aderusha/DDD-Printable-Wall-Control-System/images/Recipies/belt-clip-hanger-empty.jpg

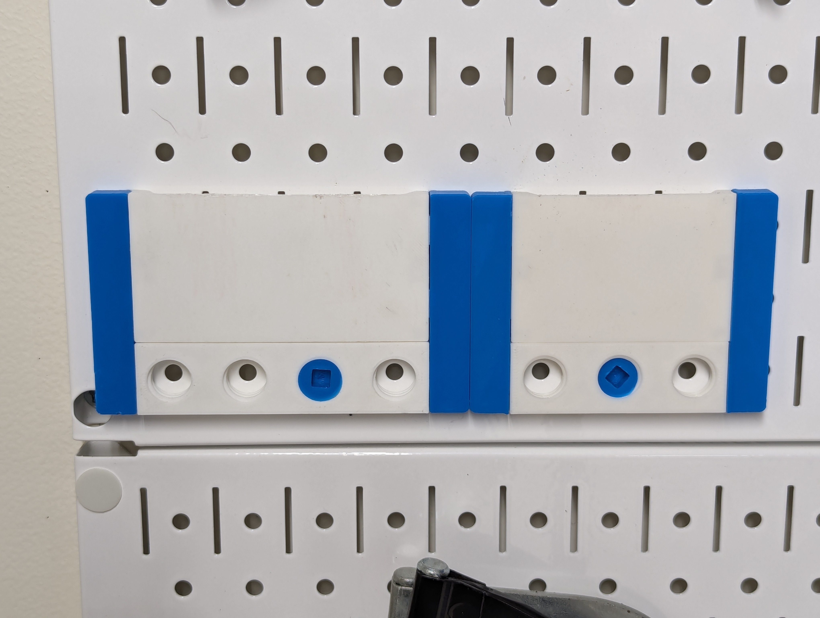
images/Recipies/belt-clip-hanger-empty.jpg
