aderusha/DDD-Printable-Wall-Control-System/images/Recipies/belt-clip-hanger-populated.jpg

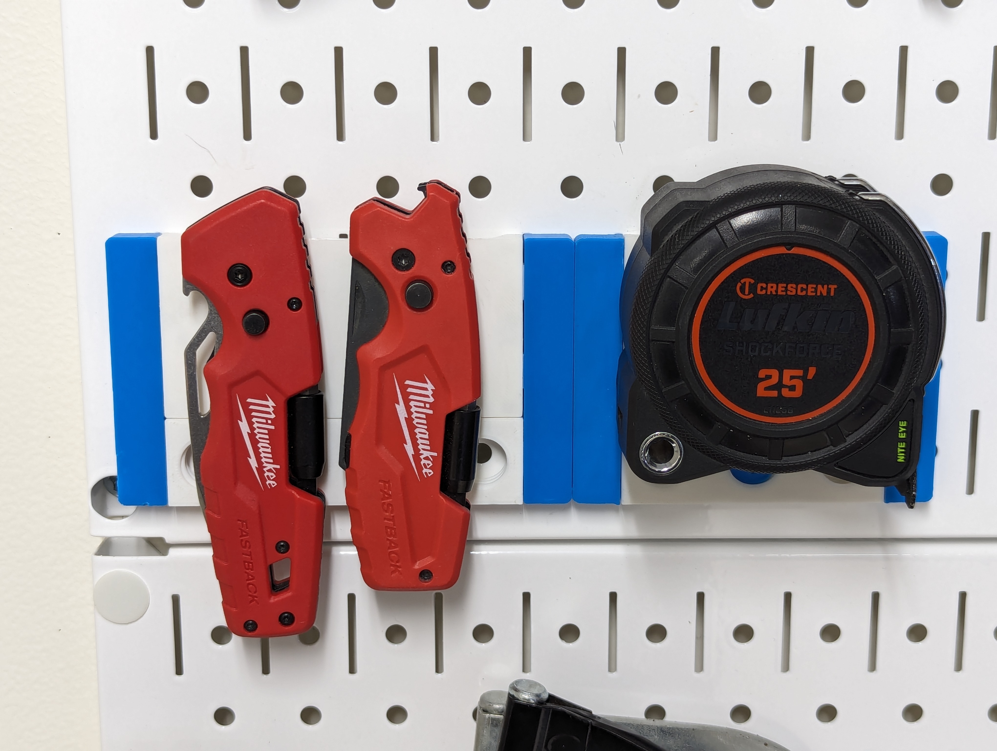
images/Recipies/belt-clip-hanger-populated.jpg
