aderusha/DDD-Printable-Wall-Control-System/images/Recipies/DeWalt-DCF923-populated.jpg

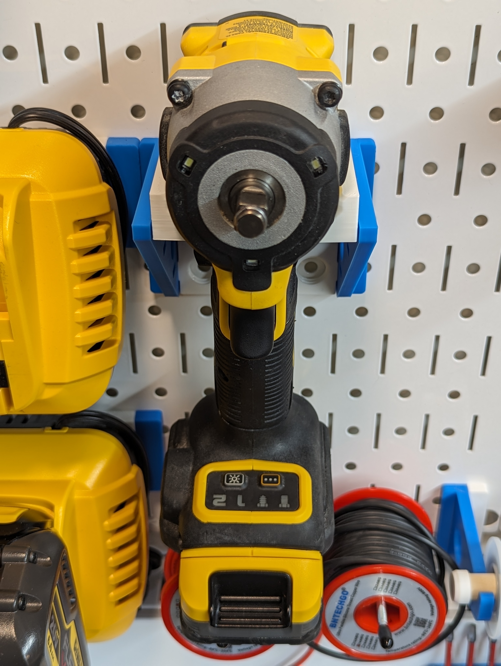
images/Recipies/DeWalt-DCF923-populated.jpg
