aderusha/DDD-Printable-Wall-Control-System/images/Vertical_vs_Horizontal_Wall_Control_Patterns.png

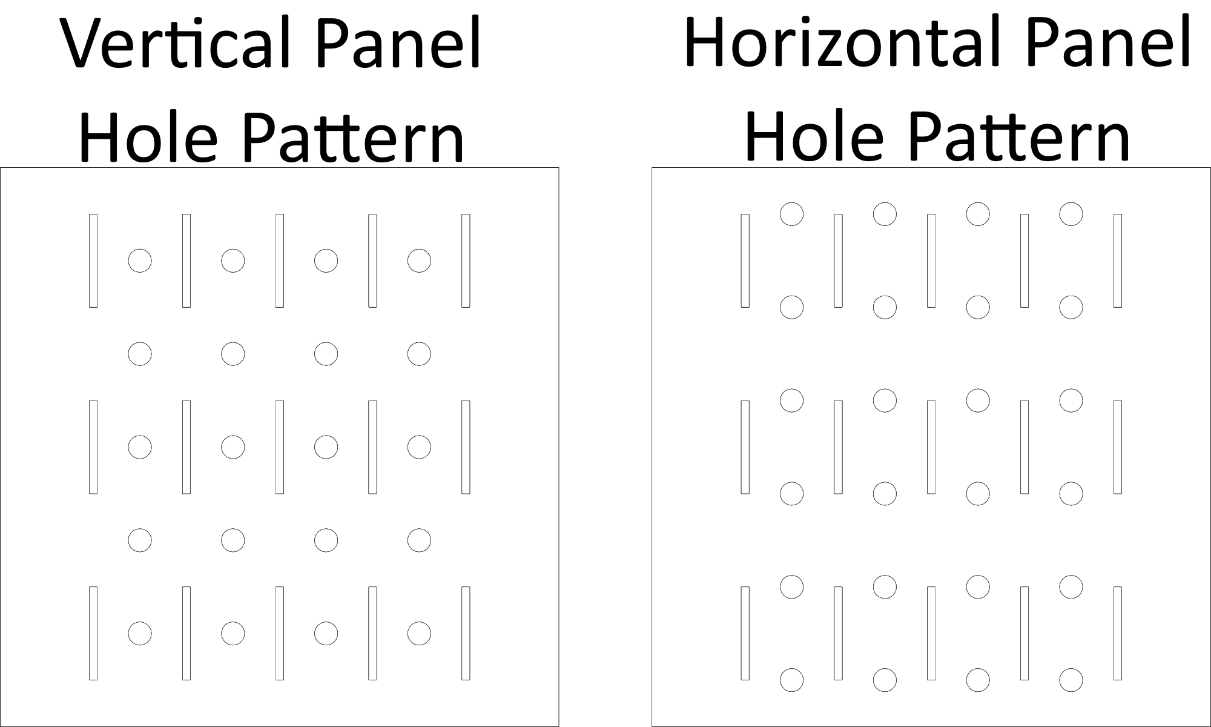
images/Vertical_vs_Horizontal_Wall_Control_Patterns.png
