aderusha/DDD-Printable-Wall-Control-System/images/WallControls-HuskyDrivers.jpg

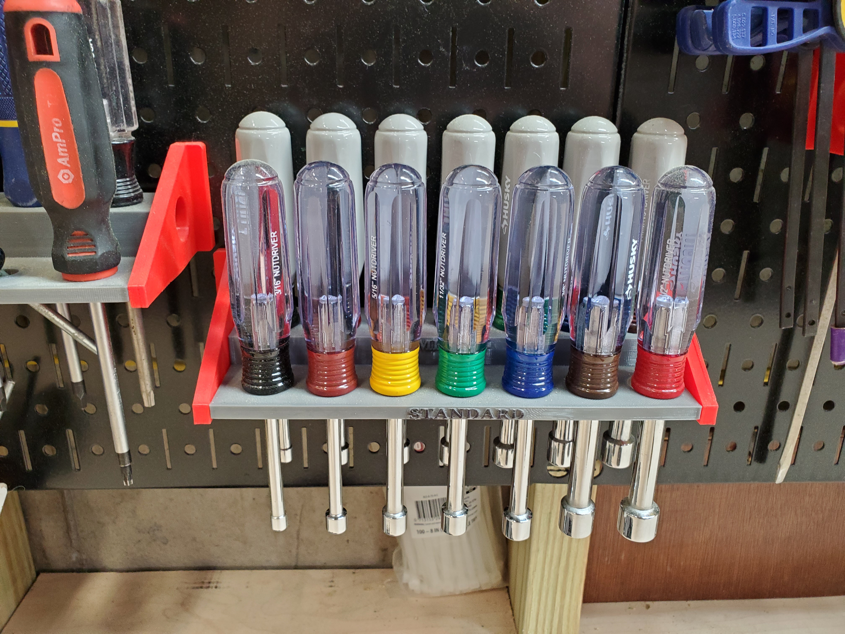
images/WallControls-HuskyDrivers.jpg
