aderusha/DDD-Printable-Wall-Control-System/images/WallControls-Irwin.jpg

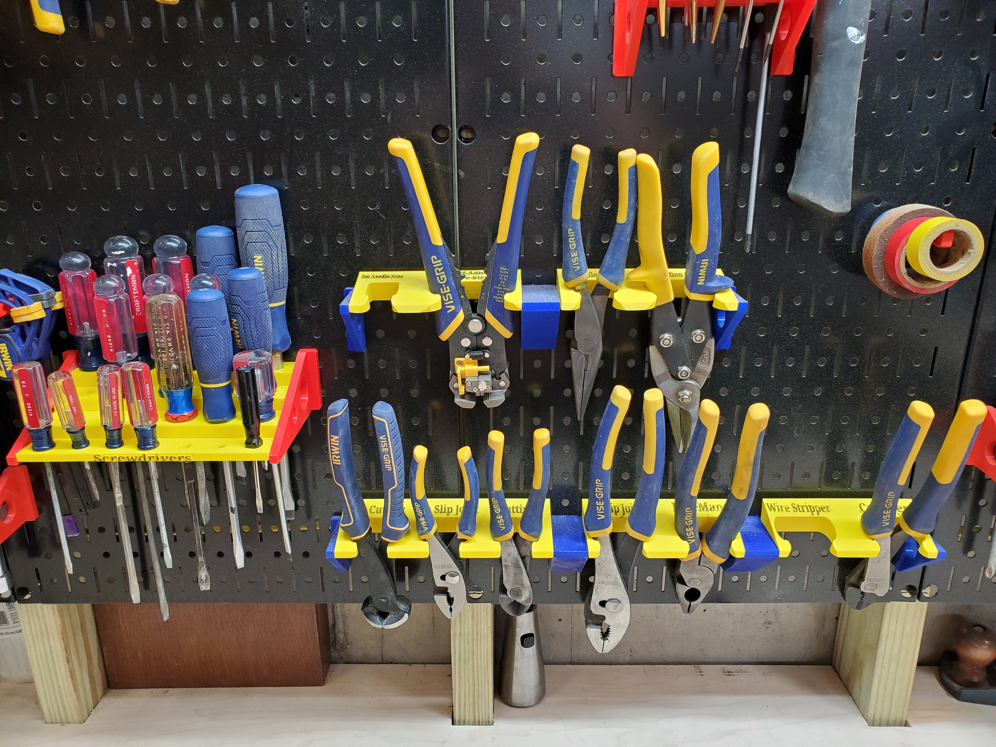
images/WallControls-Irwin.jpg
