aderusha/DDD-Printable-Wall-Control-System/images/WallOfDewalt.jpg

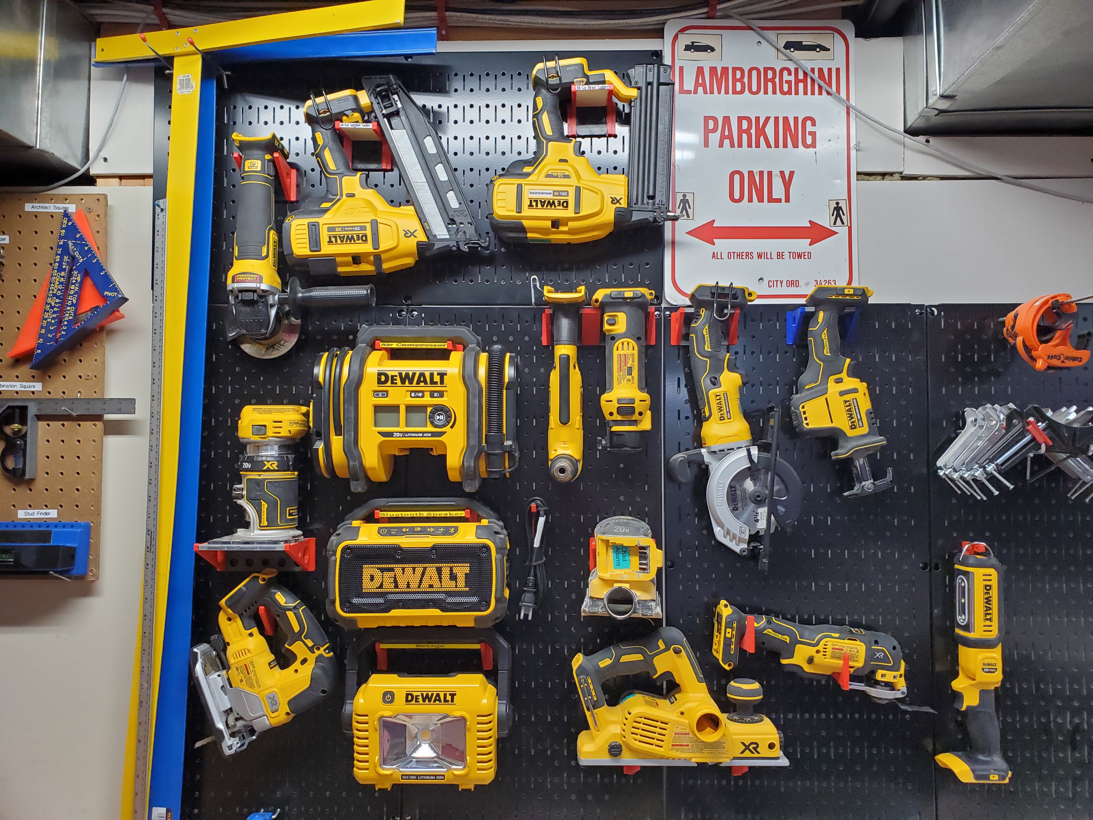
images/WallOfDewalt.jpg
