aderusha/DDD-Printable-Wall-Control-System/Sidepieces/Dowel_rod_hanger/2x2 3-4in Dowel Rod Hanger Left.stl

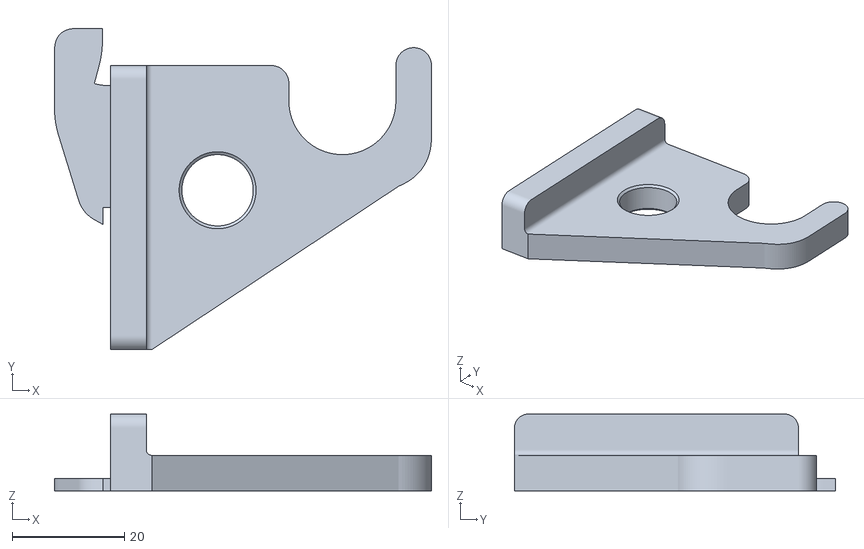
[picture p36: CAD file, 2024-03-11]
Sidepieces/Dowel_rod_hanger/2x2 3-4in Dowel Rod Hanger Left.stl
67.2 x 57.2 x 13.7
