aderusha/DDD-Printable-Wall-Control-System/Sidepieces/Flats/1x0 Flat Right.stl

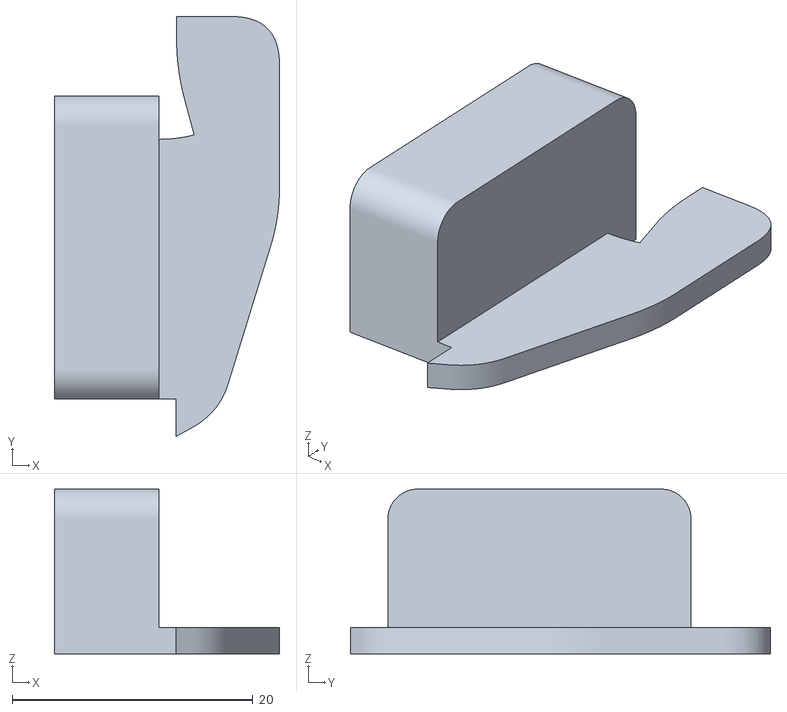
[picture p37: CAD file, 2024-03-24]
Sidepieces/Flats/1x0 Flat Right.stl
18.7 x 34.9 x 13.7
