aderusha/DDD-Printable-Wall-Control-System/Sidepieces/L_brackets/2x2 L Bracket Flat 2 Tier Right.stl

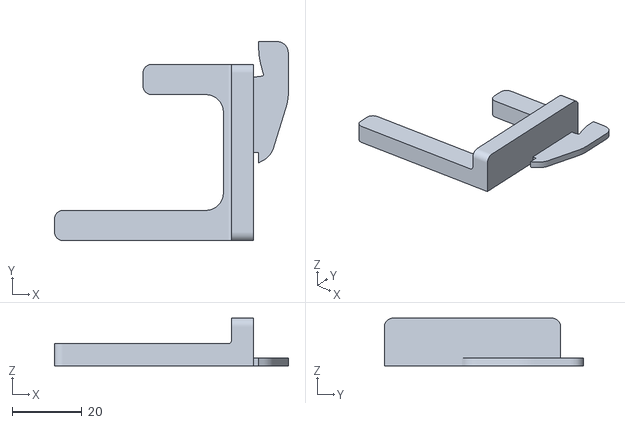
[picture p38: CAD file, 2024-07-16]
Sidepieces/L_brackets/2x2 L Bracket Flat 2 Tier Right.stl
67.1 x 57.2 x 13.7
