aderusha/DDD-Printable-Wall-Control-System/Sidepieces/Retainers/3x1 Locking Retainer for Horizontal Wall Control.stl

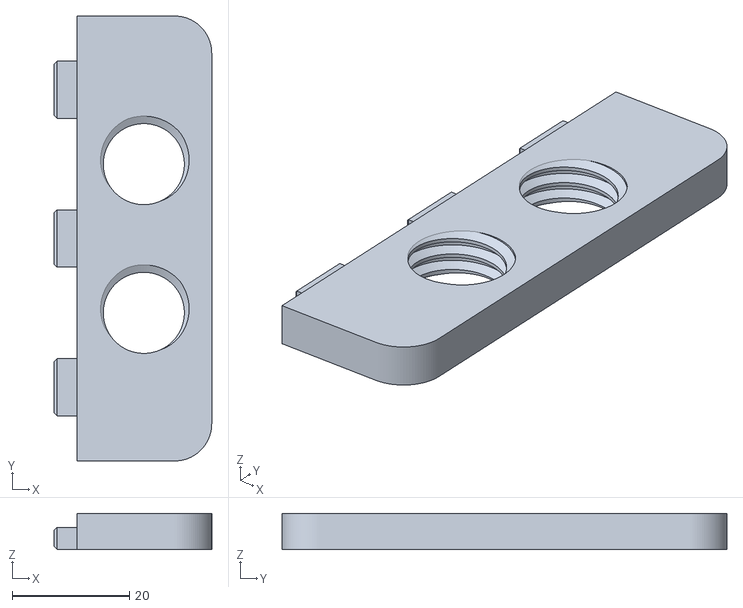
[picture p39: CAD file, 2021-11-18]
Sidepieces/Retainers/3x1 Locking Retainer for Horizontal Wall Control.stl
26.9 x 76.0 x 6.15
