aderusha/DDD-Printable-Wall-Control-System/Sidepieces/Square_brackets/3x3 Square Bracket Flat Center.stl

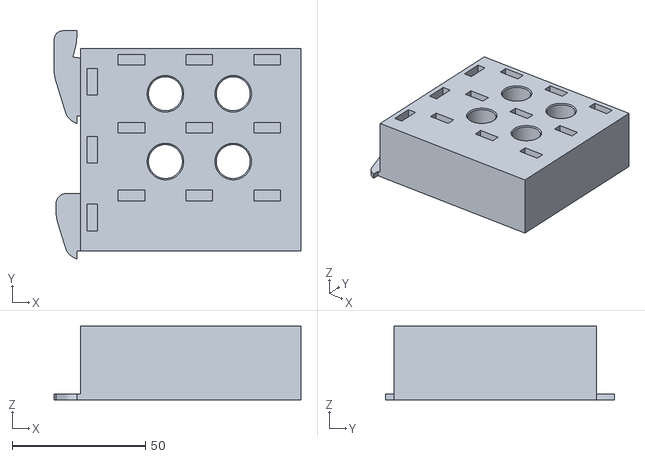
[picture p40: CAD file, 2022-08-01]
Sidepieces/Square_brackets/3x3 Square Bracket Flat Center.stl
92.6 x 85.7 x 27.6
