aderusha/DDD-Printable-Wall-Control-System/Sources/FreeCAD/Spacers.FCStd

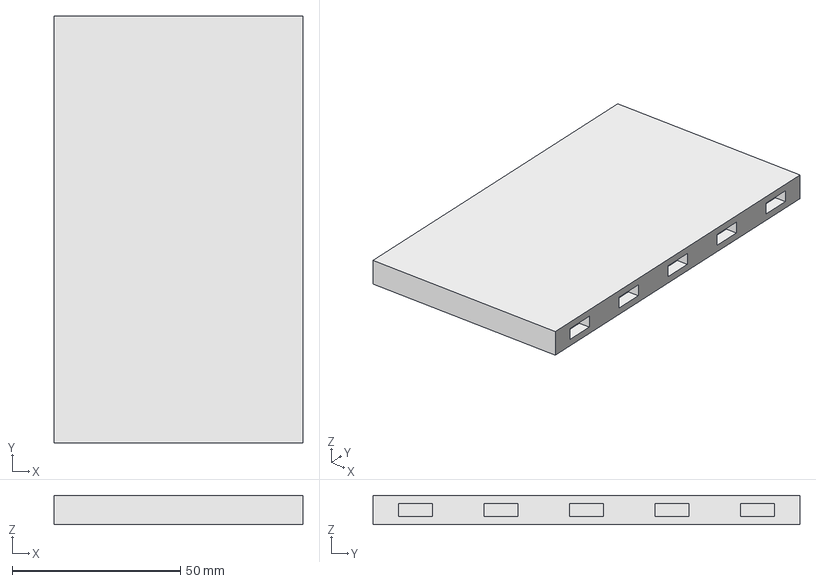
[picture p43: CAD file, 2024-07-16]
Sources/FreeCAD/Spacers.FCStd
73.8 x 126.8 x 8.70 mm
