aderusha/DDD-Printable-Wall-Control-System/Sources/Step/Parametric Centerpiece Template.step

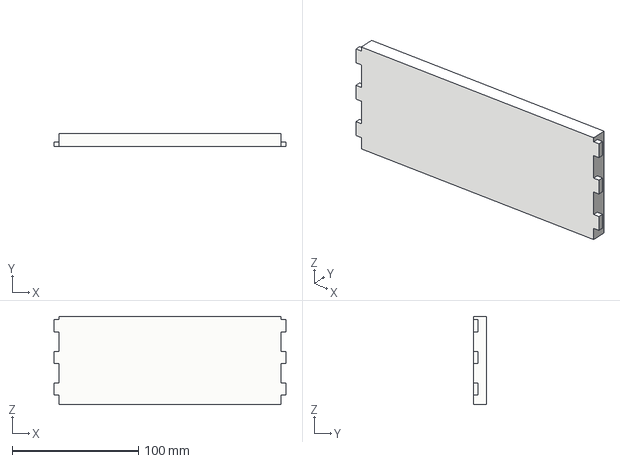
[picture p44: CAD file, 2022-11-28]
Sources/Step/Parametric Centerpiece Template.step
183.6 x 10.0 x 70.0 mm
