aderusha/DDD-Printable-Wall-Control-System/Centerpieces/Gridfinity/2x14 Gridfinity Frame 1x8.stl

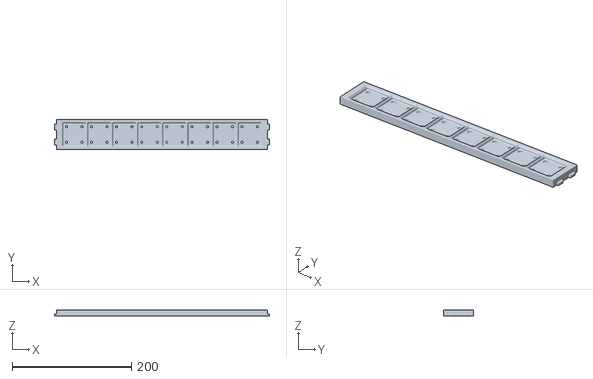
[picture p45: CAD file, 2023-10-14]
Centerpieces/Gridfinity/2x14 Gridfinity Frame 1x8.stl
360.0 x 50.6 x 10.8
