aderusha/DDD-Printable-Wall-Control-System/Centerpieces/Honeycomb_Storage_Wall/6x8 Honeycomb Storage Wall.stl

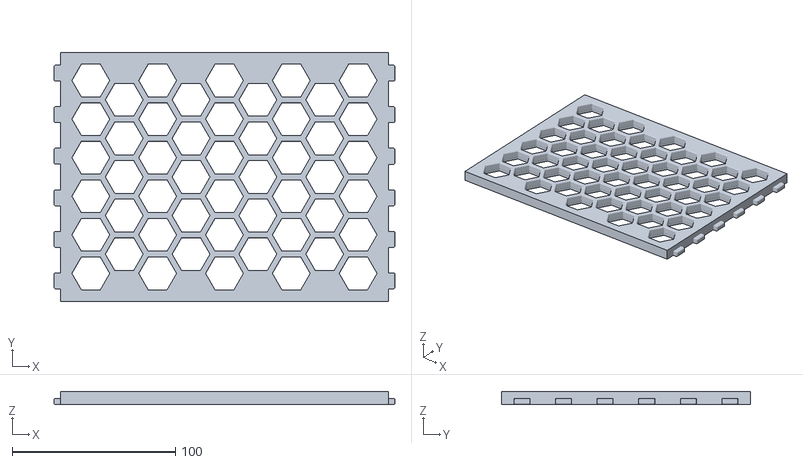
[picture p46: CAD file, 2024-07-16]
Centerpieces/Honeycomb_Storage_Wall/6x8 Honeycomb Storage Wall.stl
208.6 x 152.2 x 8.00
