aderusha/DDD-Printable-Wall-Control-System/Centerpieces/Locking_spacer/1x13 Locking Spacer.stl

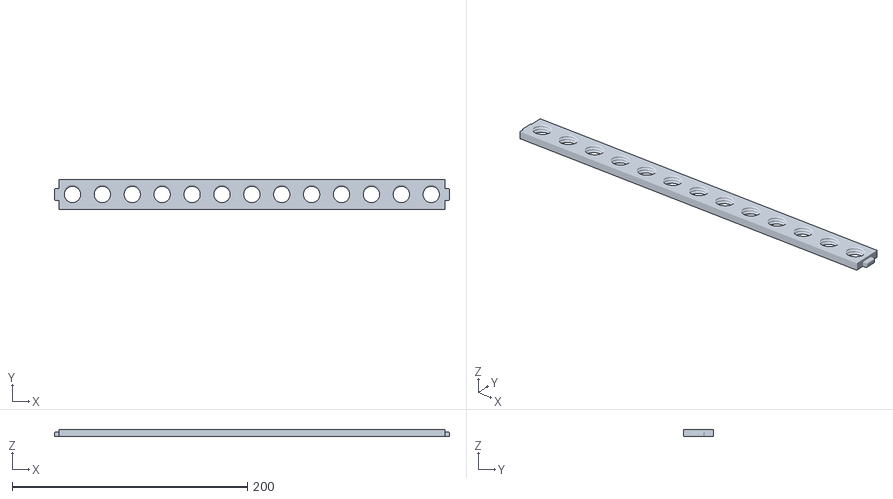
[picture p47: CAD file, 2023-10-14]
Centerpieces/Locking_spacer/1x13 Locking Spacer.stl
335.6 x 25.2 x 6.15
