aderusha/DDD-Printable-Wall-Control-System/Centerpieces/Locking_spacer_for_horizontal_Wall_Control/2x1 Locking Spacer for horizontal Wall Control.stl

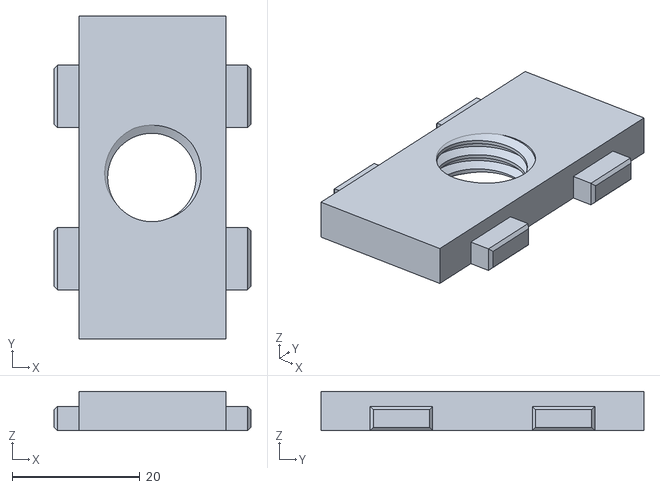
[picture p48: CAD file, 2021-11-18]
Centerpieces/Locking_spacer_for_horizontal_Wall_Control/2x1 Locking Spacer for horizontal Wall Control.stl
30.8 x 50.6 x 6.15
