aderusha/DDD-Printable-Wall-Control-System/Centerpieces/Spacer_blank/4x7 Spacer blank.stl

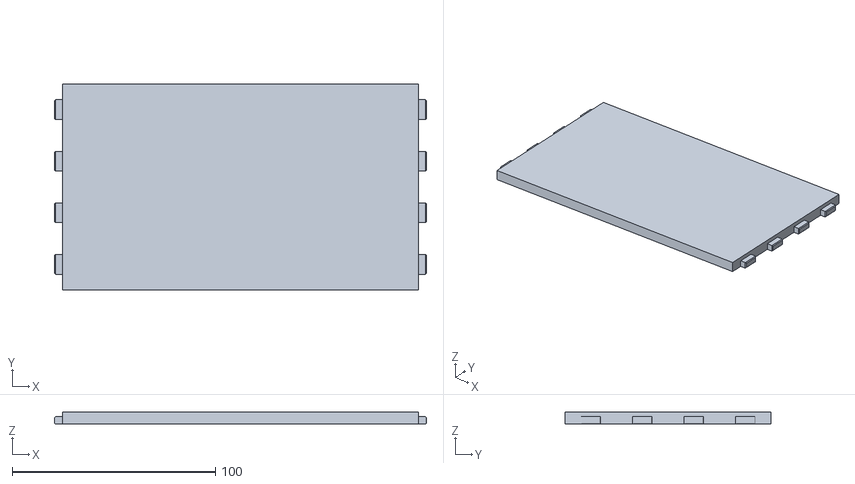
[picture p49: CAD file, 2021-10-13]
Centerpieces/Spacer_blank/4x7 Spacer blank.stl
183.2 x 101.4 x 6.15
