aderusha/DDD-Printable-Wall-Control-System/Centerpieces/Spacer_blank_flush/2x10 Spacer blank flush.stl

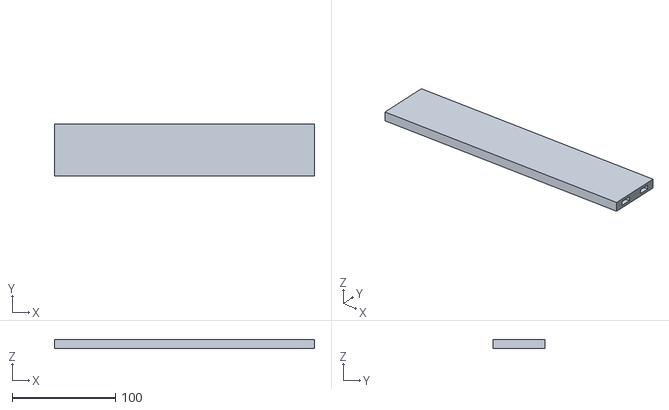
[picture p50: CAD file, 2023-03-14]
Centerpieces/Spacer_blank_flush/2x10 Spacer blank flush.stl
251.6 x 50.6 x 8.70
