aderusha/DDD-Printable-Wall-Control-System/Centerpieces/Spacer_clip-on/3x3 Spacer clip-on.stl

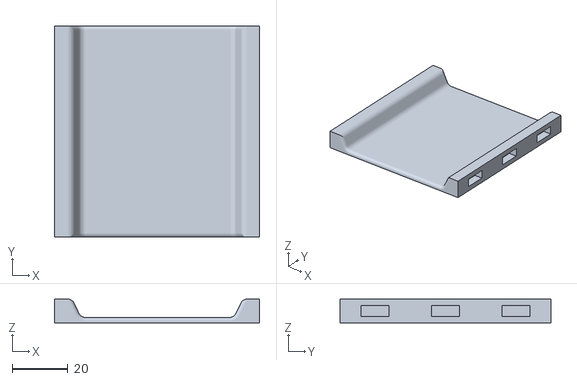
[picture p51: CAD file, 2020-11-09]
Centerpieces/Spacer_clip-on/3x3 Spacer clip-on.stl
73.8 x 76.0 x 8.60
