aderusha/DDD-Printable-Wall-Control-System/Centerpieces/Spacer_perforated/2x6 Spacer perforated.stl

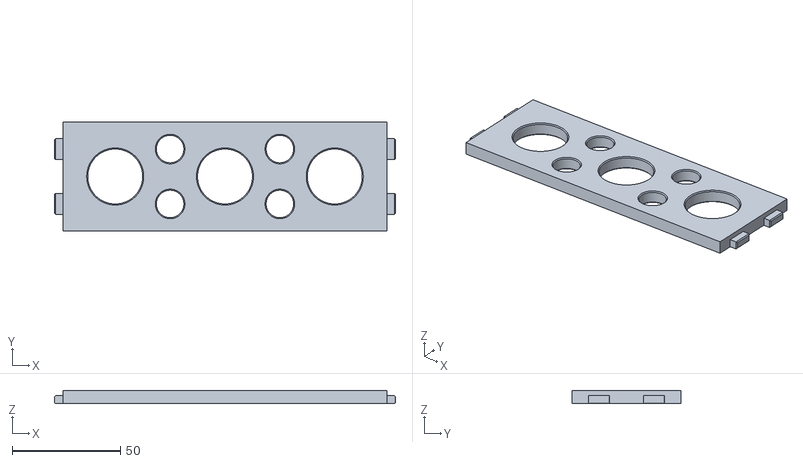
[picture p52: CAD file, 2020-11-09]
Centerpieces/Spacer_perforated/2x6 Spacer perforated.stl
157.8 x 50.6 x 6.15
