aderusha/DDD-Printable-Wall-Control-System/Centerpieces/U_hooks/2x2 1.5in U hook catch.stl

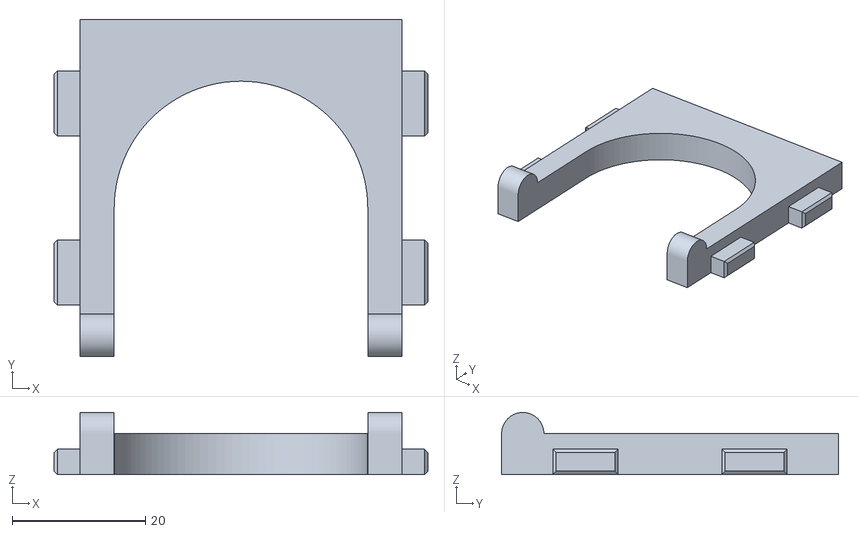
[picture p54: CAD file, 2021-11-23]
Centerpieces/U_hooks/2x2 1.5in U hook catch.stl
56.2 x 50.6 x 9.33
