aderusha/DDD-Printable-Wall-Control-System/Quickhooks/Quickhook Lockable Retainer.stl

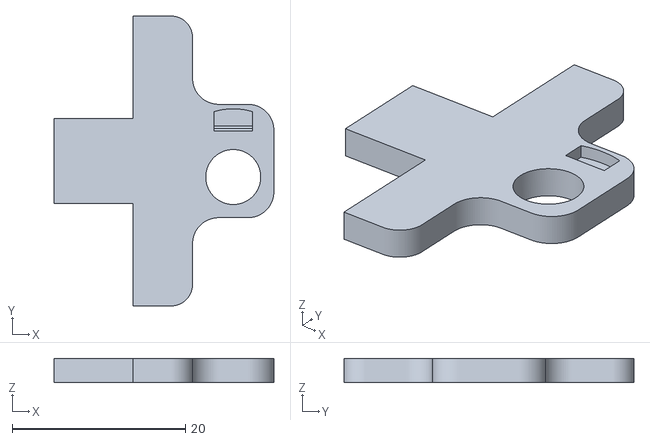
[picture p55: CAD file, 2024-07-16]
Quickhooks/Quickhook Lockable Retainer.stl
25.4 x 33.5 x 2.80
