aderusha/DDD-Printable-Wall-Control-System/Sidepieces/Angle_brackets/3x3 Angle Bracket Flat Center.stl

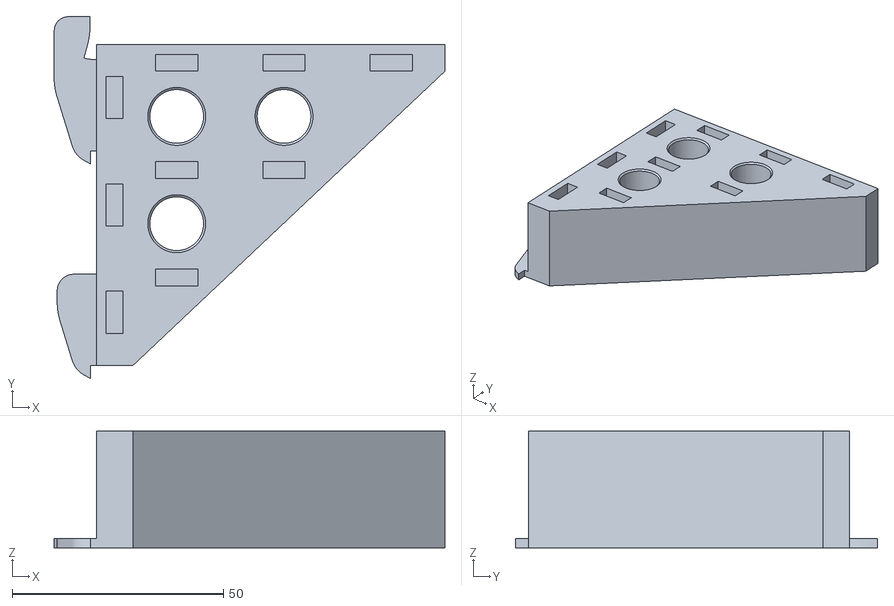
[picture p56: CAD file, 2024-01-18]
Sidepieces/Angle_brackets/3x3 Angle Bracket Flat Center.stl
92.6 x 85.7 x 27.6
