aderusha/DDD-Printable-Wall-Control-System/Sidepieces/Angle_brackets1/2x2 Angle Bracket Right.stl

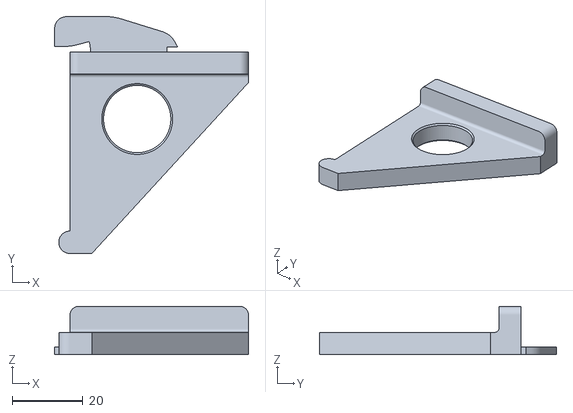
[picture p57: CAD file, 2020-11-10]
Sidepieces/Angle_brackets1/2x2 Angle Bracket Right.stl
55.0 x 67.2 x 13.7
