aderusha/DDD-Printable-Wall-Control-System/Sidepieces/Retainers/2x1 Locking Retainer for Horizontal Wall Control.stl

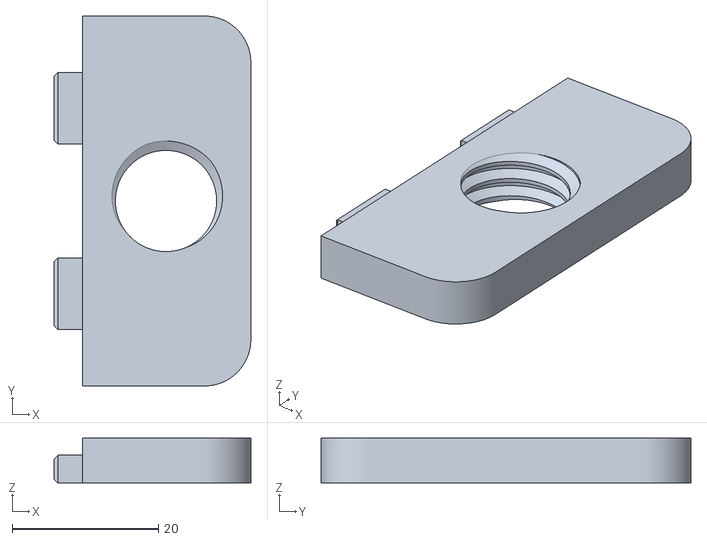
[picture p58: CAD file, 2021-11-18]
Sidepieces/Retainers/2x1 Locking Retainer for Horizontal Wall Control.stl
26.9 x 50.6 x 6.15
