aderusha/DDD-Printable-Wall-Control-System/Sidepieces/Square_brackets/3x3 Square Bracket Flat Left.stl

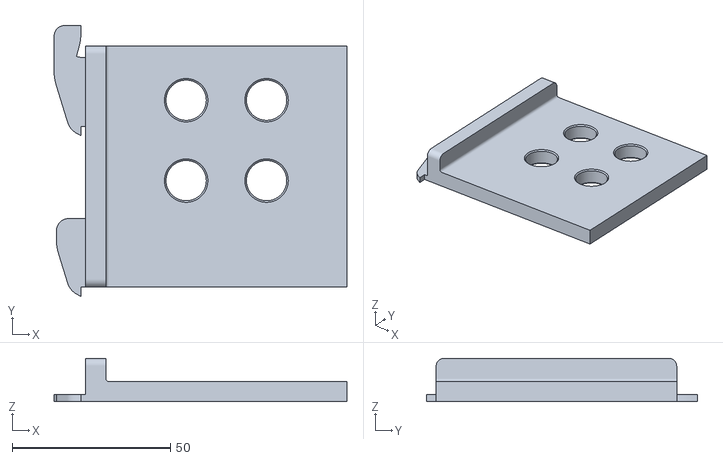
[picture p59: CAD file, 2022-08-01]
Sidepieces/Square_brackets/3x3 Square Bracket Flat Left.stl
92.6 x 85.7 x 13.7
