aderusha/DDD-Printable-Wall-Control-System/Sidepieces/Strap_mounts/2x0 30mm Strap Right.stl

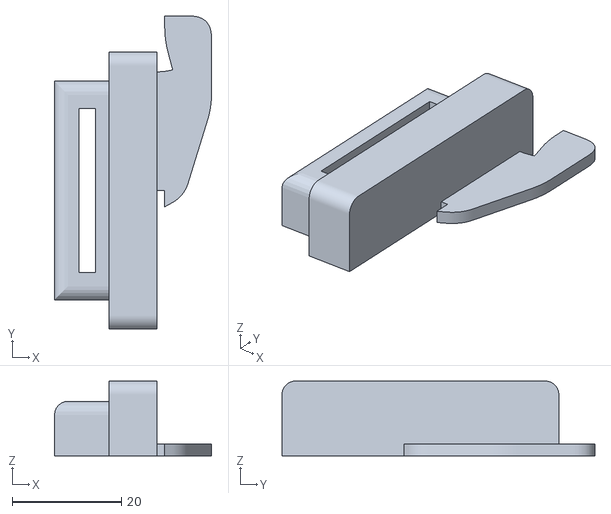
[picture p60: CAD file, 2022-08-23]
Sidepieces/Strap_mounts/2x0 30mm Strap Right.stl
28.7 x 57.2 x 13.7
