aderusha/DDD-Printable-Wall-Control-System/Sidepieces/U_brackets/2x2 U Bracket 3-4in Hook Center.stl

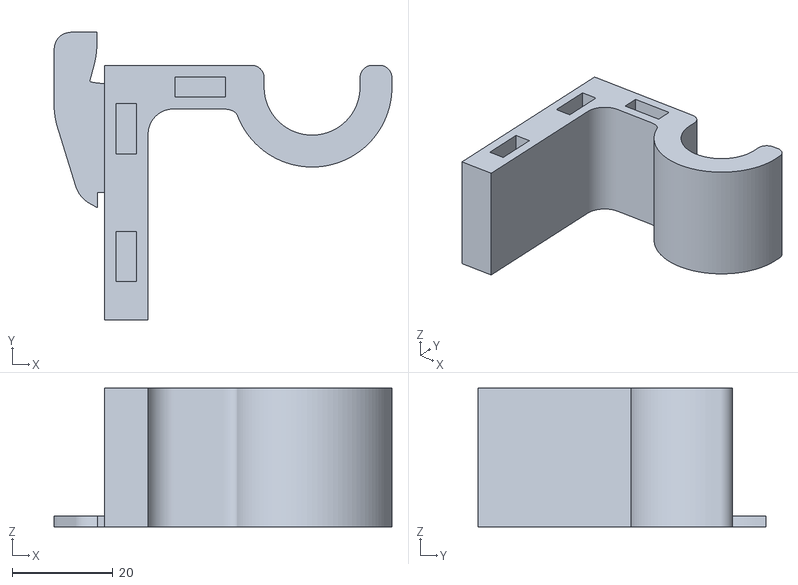
[picture p61: CAD file, 2024-03-11]
Sidepieces/U_brackets/2x2 U Bracket 3-4in Hook Center.stl
67.2 x 57.2 x 27.6
