aderusha/DDD-Printable-Wall-Control-System/Sources/FreeCAD/Quickhooks.FCStd

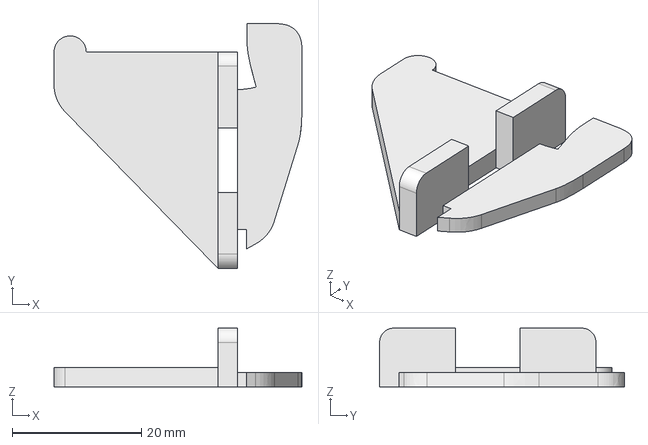
[picture p62: CAD file, 2022-07-24]
Sources/FreeCAD/Quickhooks.FCStd
38.4 x 37.9 x 9.10 mm
