aderusha/DDD-Printable-Wall-Control-System/Sources/Step/Parametric Centerpiece Divider Rack Template.step

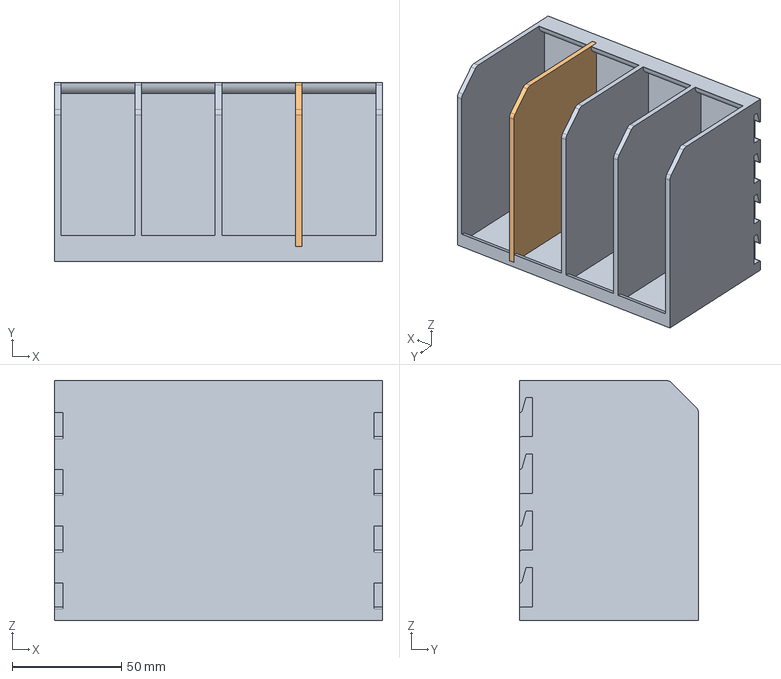
[picture p63: CAD file, 2022-11-28]
Sources/Step/Parametric Centerpiece Divider Rack Template.step
150.2 x 82.0 x 110.0 mm
