aderusha/DDD-Printable-Wall-Control-System/Centerpieces/Gridfinity/2x10 Gridfinity Frame 1x6.stl

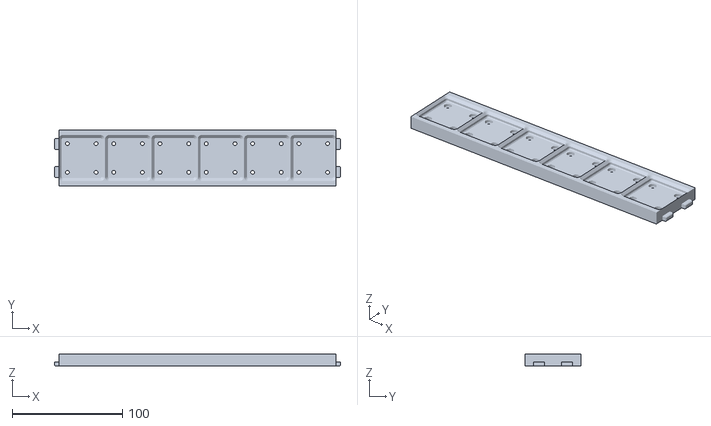
[picture p64: CAD file, 2023-10-14]
Centerpieces/Gridfinity/2x10 Gridfinity Frame 1x6.stl
259.4 x 50.7 x 10.8
