aderusha/DDD-Printable-Wall-Control-System/Centerpieces/Honeycomb_Storage_Wall/6x6 Honeycomb Storage Wall.stl

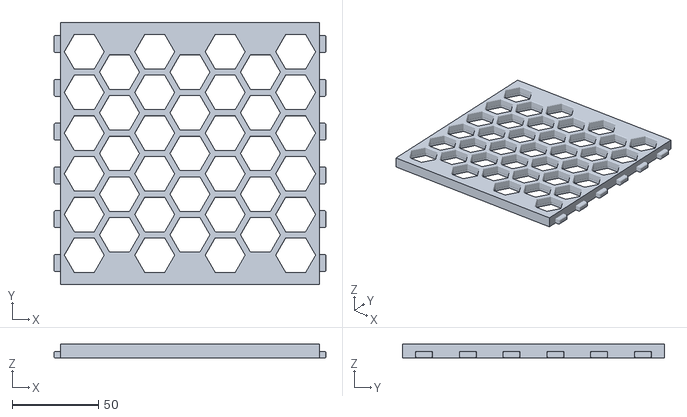
[picture p65: CAD file, 2024-07-16]
Centerpieces/Honeycomb_Storage_Wall/6x6 Honeycomb Storage Wall.stl
157.8 x 152.2 x 8.00
