aderusha/DDD-Printable-Wall-Control-System/Centerpieces/Locking_spacer/1x14 Locking Spacer.stl

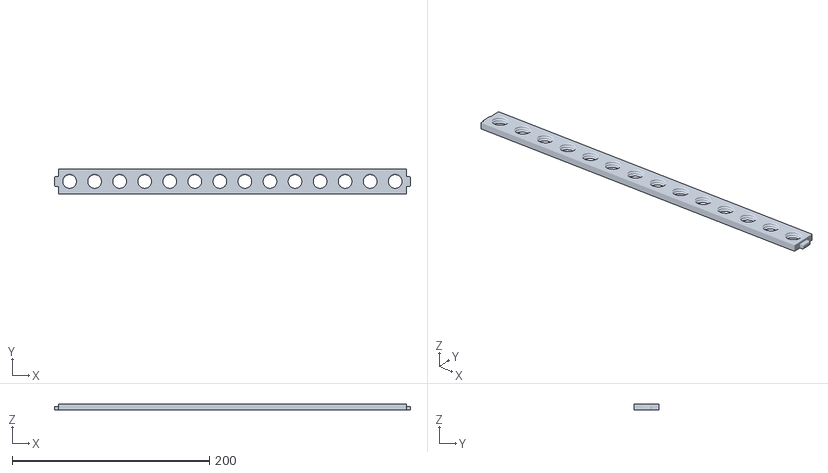
[picture p66: CAD file, 2023-10-14]
Centerpieces/Locking_spacer/1x14 Locking Spacer.stl
361.0 x 25.2 x 6.15
