aderusha/DDD-Printable-Wall-Control-System/Centerpieces/Spacer_blank/4x5 Spacer blank.stl

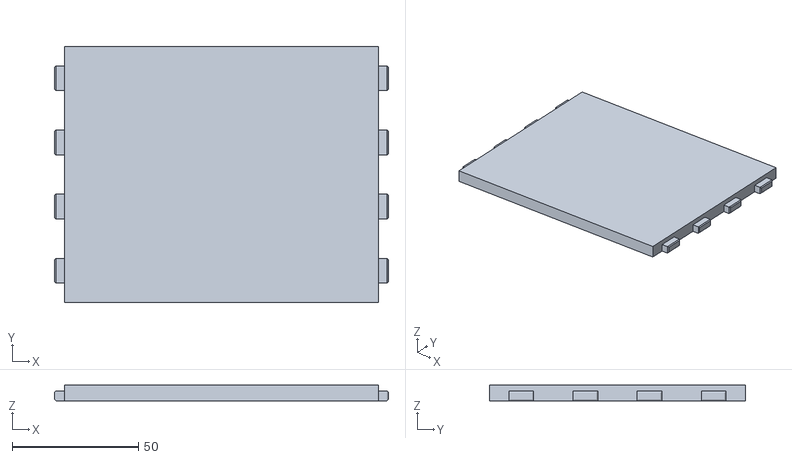
[picture p68: CAD file, 2021-10-13]
Centerpieces/Spacer_blank/4x5 Spacer blank.stl
132.4 x 101.4 x 6.15
