aderusha/DDD-Printable-Wall-Control-System/Centerpieces/Spacer_blank_flush/2x8 Spacer blank flush.stl

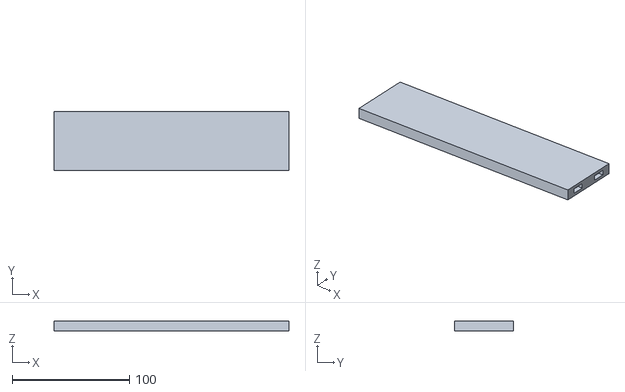
[picture p69: CAD file, 2023-03-14]
Centerpieces/Spacer_blank_flush/2x8 Spacer blank flush.stl
200.8 x 50.6 x 8.70
