aderusha/DDD-Printable-Wall-Control-System/Centerpieces/Spacer_clip-on/2x7 Spacer clip-on.stl

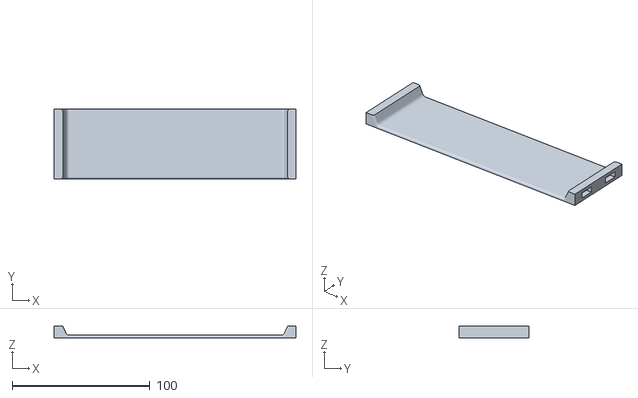
[picture p70: CAD file, 2020-11-09]
Centerpieces/Spacer_clip-on/2x7 Spacer clip-on.stl
175.4 x 50.6 x 8.60
