aderusha/DDD-Printable-Wall-Control-System/Centerpieces/Spacer_perforated/2x5 Spacer perforated.stl

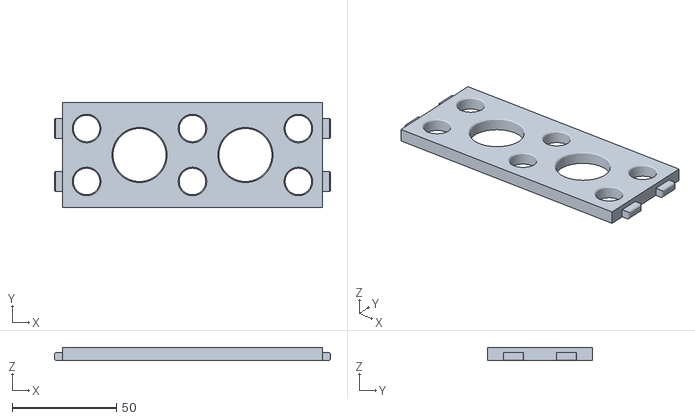
[picture p71: CAD file, 2020-11-09]
Centerpieces/Spacer_perforated/2x5 Spacer perforated.stl
132.4 x 50.6 x 6.15
