aderusha/DDD-Printable-Wall-Control-System/Centerpieces/Tool_hooks/6x9 Titan 148-Piece Master Security Bit Set - Top.stl

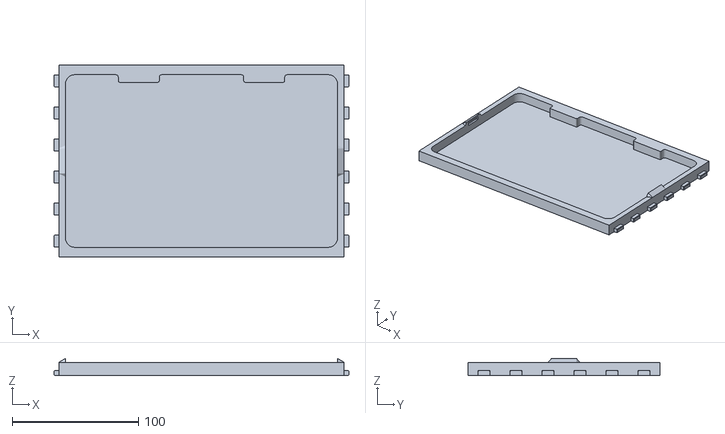
[picture p72: CAD file, 2024-01-23]
Centerpieces/Tool_hooks/6x9 Titan 148-Piece Master Security Bit Set - Top.stl
234.0 x 152.2 x 13.5
