aderusha/DDD-Printable-Wall-Control-System/Centerpieces/U_hooks/2x2 30mm U hook.stl

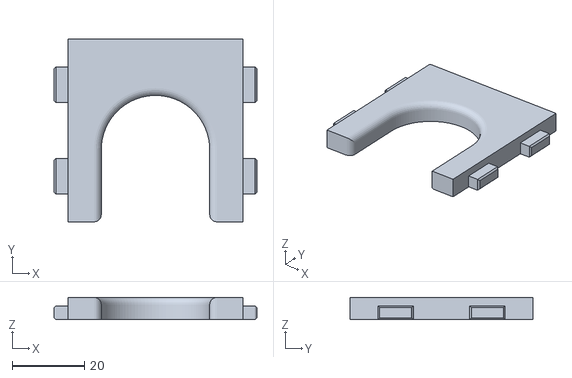
[picture p73: CAD file, 2021-11-23]
Centerpieces/U_hooks/2x2 30mm U hook.stl
56.2 x 50.6 x 6.15
