aderusha/DDD-Printable-Wall-Control-System/Quickhooks/Quickhook Lock Peg.stl

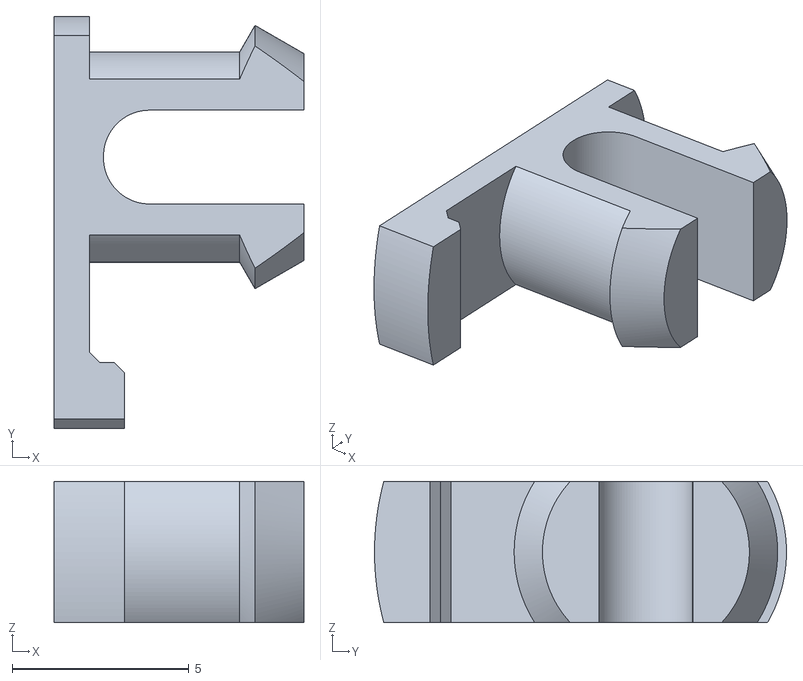
[picture p74: CAD file, 2024-07-16]
Quickhooks/Quickhook Lock Peg.stl
7.07 x 11.7 x 4.00
