aderusha/DDD-Printable-Wall-Control-System/Sidepieces/Angle_brackets/3x3 Angle Bracket Flat Left.stl

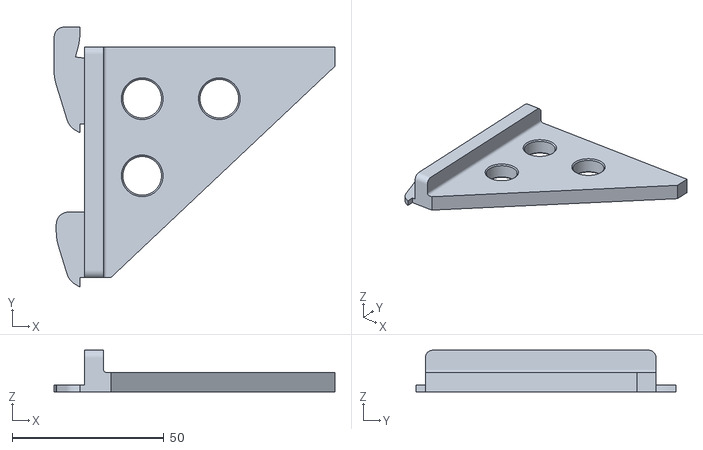
[picture p75: CAD file, 2024-01-18]
Sidepieces/Angle_brackets/3x3 Angle Bracket Flat Left.stl
92.6 x 85.7 x 13.7
