aderusha/DDD-Printable-Wall-Control-System/Sidepieces/Angle_brackets1/2x3.25 Angle Bracket Inverted Right.stl

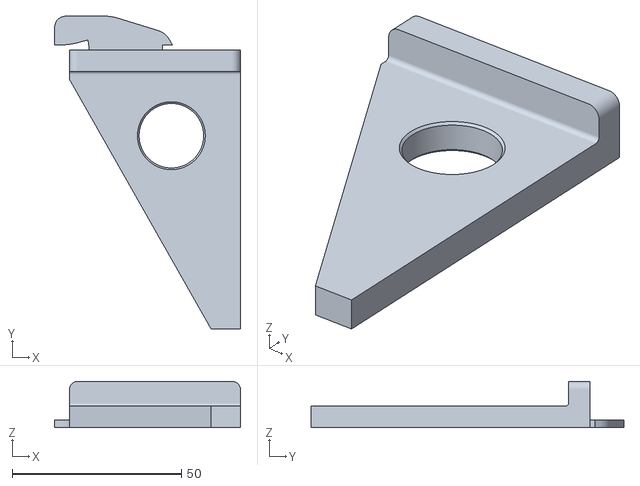
[picture p76: CAD file, 2020-11-10]
Sidepieces/Angle_brackets1/2x3.25 Angle Bracket Inverted Right.stl
55.0 x 92.6 x 13.7
