aderusha/DDD-Printable-Wall-Control-System/Sidepieces/Dowel_rod_hanger/2x2 3-4in Dowel Rod Hanger Center.stl

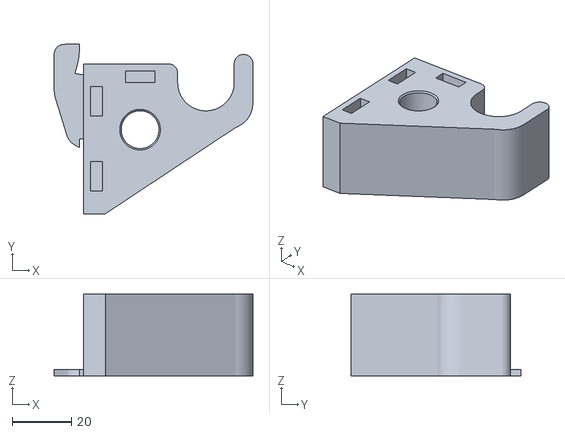
[picture p77: CAD file, 2024-03-11]
Sidepieces/Dowel_rod_hanger/2x2 3-4in Dowel Rod Hanger Center.stl
67.1 x 57.2 x 27.6
