aderusha/DDD-Printable-Wall-Control-System/Sidepieces/Flats/1x0 Flat Center.stl

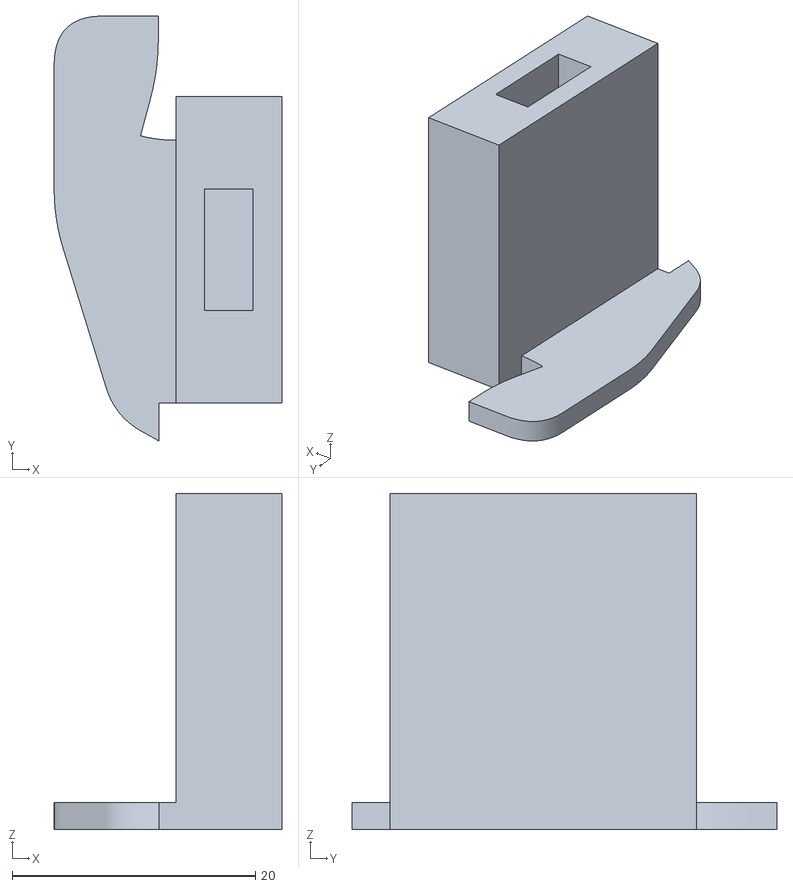
[picture p78: CAD file, 2024-03-24]
Sidepieces/Flats/1x0 Flat Center.stl
18.7 x 34.9 x 27.6
