aderusha/DDD-Printable-Wall-Control-System/Sidepieces/L_brackets/2x2 L Bracket Flat 2 Tier Center.stl

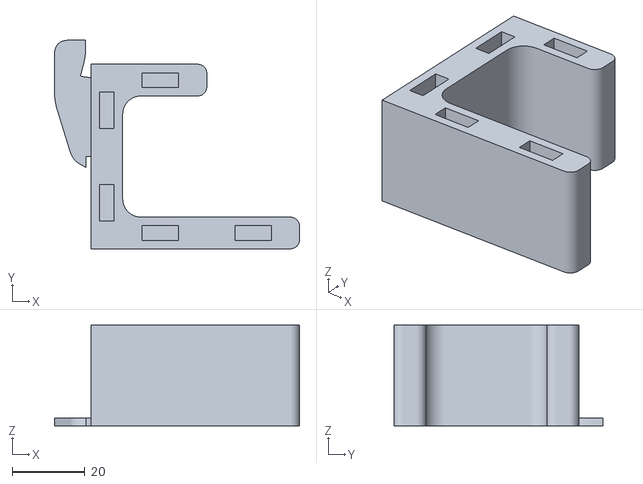
[picture p79: CAD file, 2024-07-16]
Sidepieces/L_brackets/2x2 L Bracket Flat 2 Tier Center.stl
67.1 x 57.2 x 27.6
