aderusha/DDD-Printable-Wall-Control-System/Sidepieces/Retainers/2x0 Retainer.stl

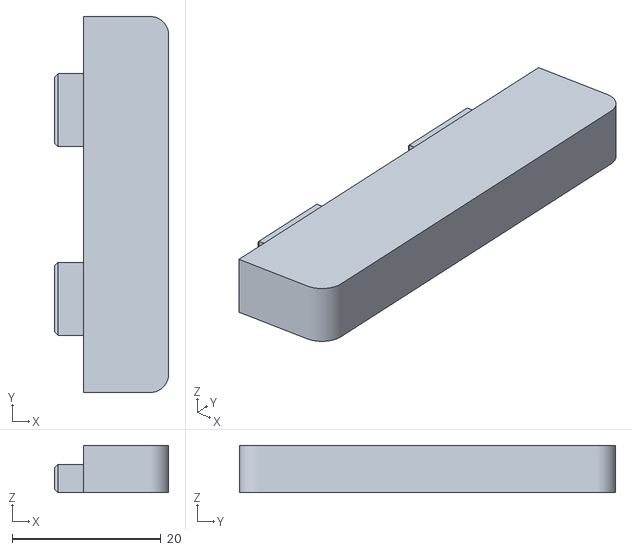
[picture p80: CAD file, 2020-12-05]
Sidepieces/Retainers/2x0 Retainer.stl
15.4 x 50.6 x 6.35
