aderusha/DDD-Printable-Wall-Control-System/Accessories/3-4in Dowel Cap.stl

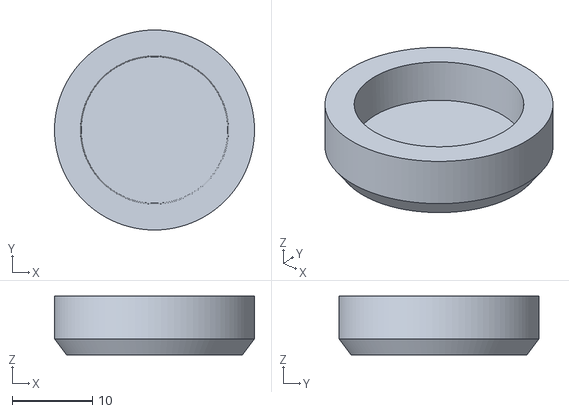
[picture p82: CAD file, 2021-01-22]
Accessories/3-4in Dowel Cap.stl
25.0 x 25.0 x 7.35
