aderusha/DDD-Printable-Wall-Control-System/Centerpieces/Gridfinity/5x2 Gridfinity Frame 3x1.stl

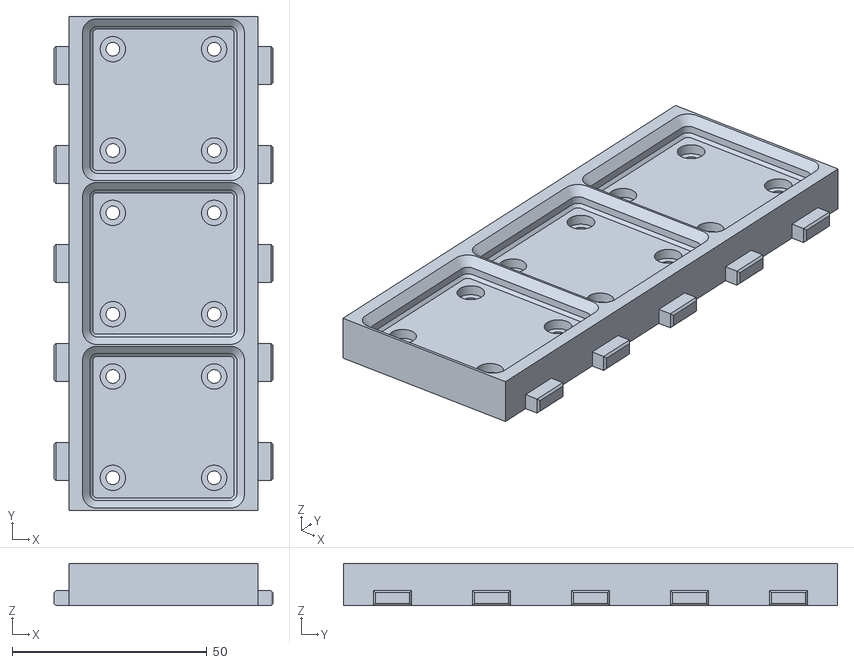
[picture p83: CAD file, 2022-08-01]
Centerpieces/Gridfinity/5x2 Gridfinity Frame 3x1.stl
56.2 x 126.8 x 10.8
