aderusha/DDD-Printable-Wall-Control-System/Centerpieces/Locking_spacer/1x10 Locking Spacer.stl

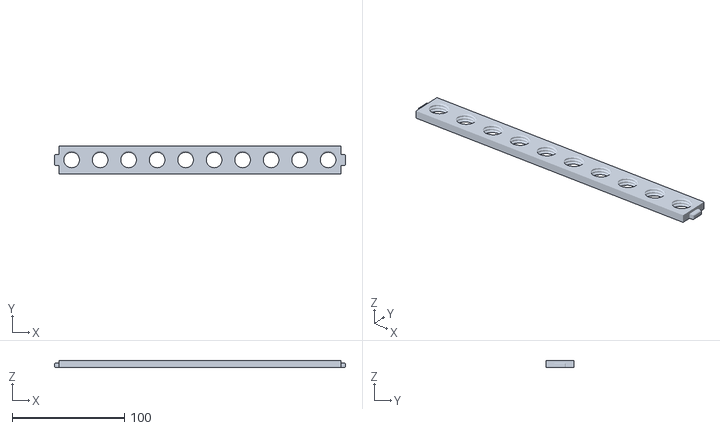
[picture p84: CAD file, 2023-10-14]
Centerpieces/Locking_spacer/1x10 Locking Spacer.stl
259.4 x 25.2 x 6.15
