aderusha/DDD-Printable-Wall-Control-System/Centerpieces/Spacer_blank/4x3 Spacer blank.stl

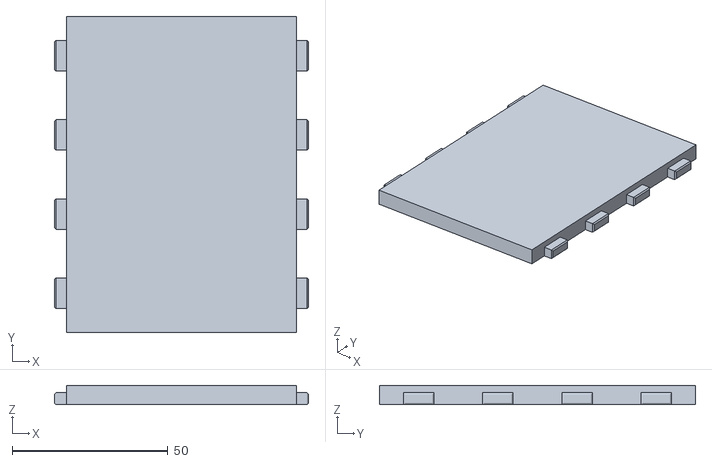
[picture p85: CAD file, 2021-10-13]
Centerpieces/Spacer_blank/4x3 Spacer blank.stl
81.6 x 101.4 x 6.15
