aderusha/DDD-Printable-Wall-Control-System/Centerpieces/Spacer_blank_flush/3x4 Spacer blank flush.stl

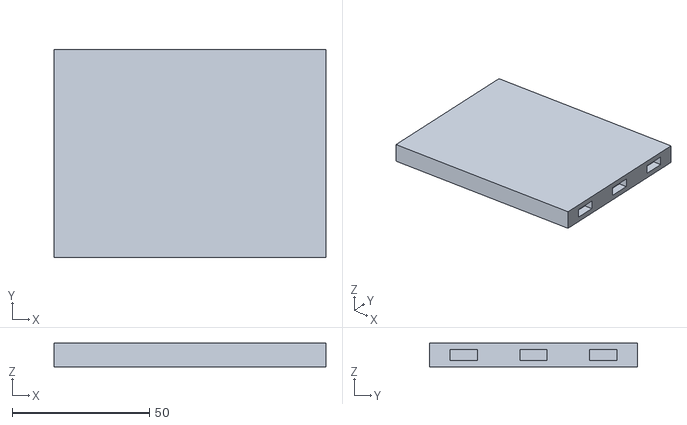
[picture p86: CAD file, 2021-11-26]
Centerpieces/Spacer_blank_flush/3x4 Spacer blank flush.stl
99.2 x 76.0 x 8.70
