aderusha/DDD-Printable-Wall-Control-System/Centerpieces/Spacer_clip-on/2x3 Spacer clip-on.stl

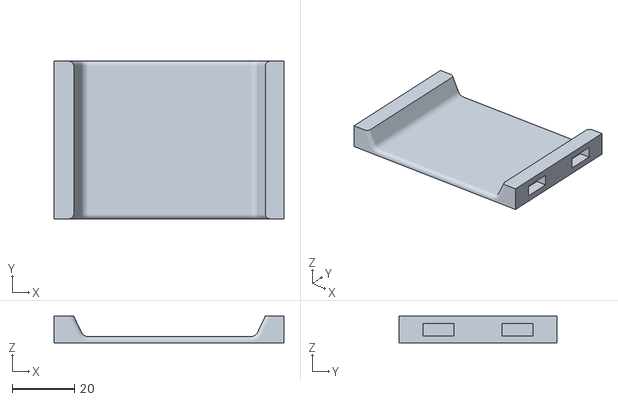
[picture p87: CAD file, 2020-11-09]
Centerpieces/Spacer_clip-on/2x3 Spacer clip-on.stl
73.8 x 50.6 x 8.60
