aderusha/DDD-Printable-Wall-Control-System/Centerpieces/Spacer_perforated/3x7 Spacer perforated.stl

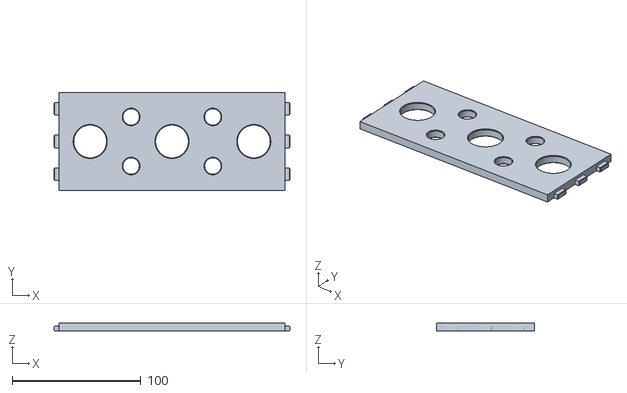
[picture p88: CAD file, 2020-11-09]
Centerpieces/Spacer_perforated/3x7 Spacer perforated.stl
183.2 x 76.0 x 6.15
