aderusha/DDD-Printable-Wall-Control-System/Centerpieces/Tool_hooks/1x2 HOMGE vice handle.stl

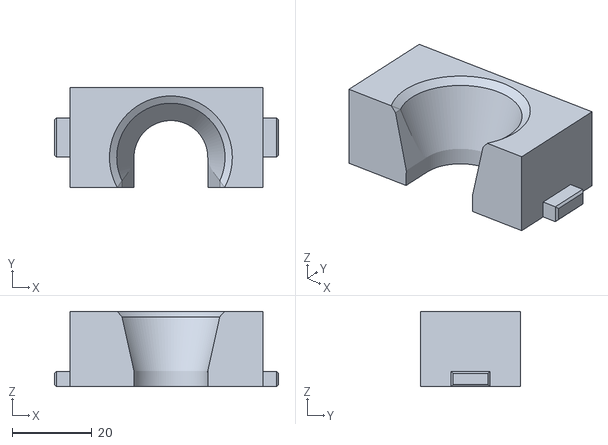
[picture p89: CAD file, 2024-01-18]
Centerpieces/Tool_hooks/1x2 HOMGE vice handle.stl
56.2 x 25.2 x 18.9
