aderusha/DDD-Printable-Wall-Control-System/Centerpieces/U_hooks/3x2 1.5in U hook catch.stl

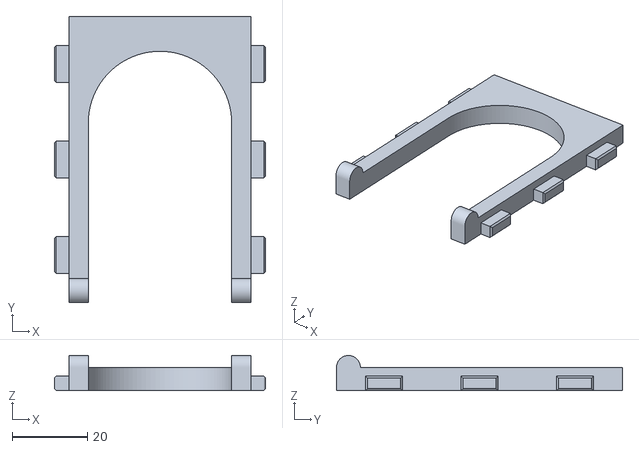
[picture p90: CAD file, 2021-11-23]
Centerpieces/U_hooks/3x2 1.5in U hook catch.stl
56.2 x 76.0 x 9.33
