aderusha/DDD-Printable-Wall-Control-System/Quickhooks/Quickhook 3in Light.stl

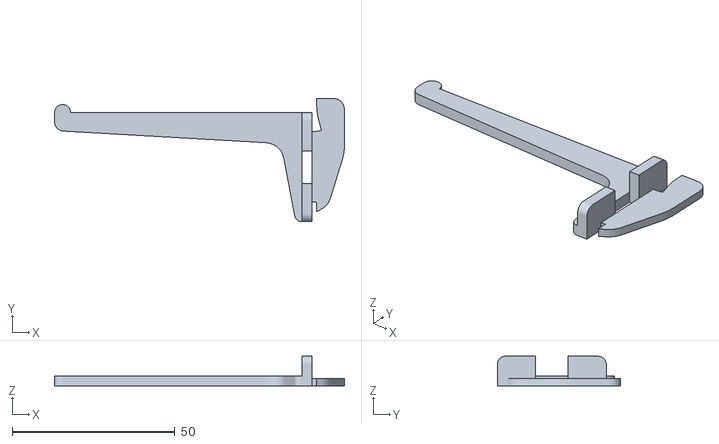
[picture p91: CAD file, 2020-11-10]
Quickhooks/Quickhook 3in Light.stl
89.2 x 37.9 x 9.10
