aderusha/DDD-Printable-Wall-Control-System/Sidepieces/Angle_brackets1/4x4 Angle Bracket Right.stl

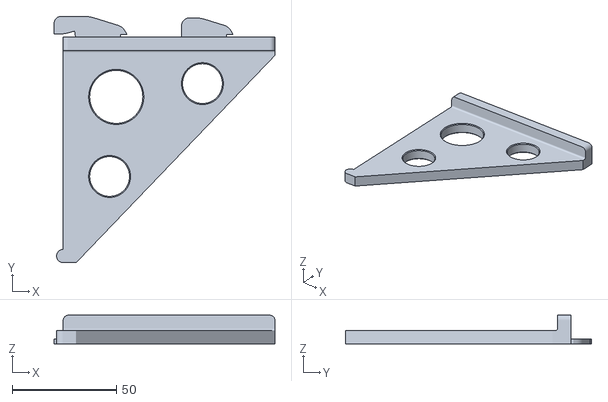
[picture p92: CAD file, 2020-11-10]
Sidepieces/Angle_brackets1/4x4 Angle Bracket Right.stl
105.8 x 118.0 x 13.7
