aderusha/DDD-Printable-Wall-Control-System/Sidepieces/Dowel_rod_hanger/2x4 3-4in Dowel Rod Hanger Left.stl

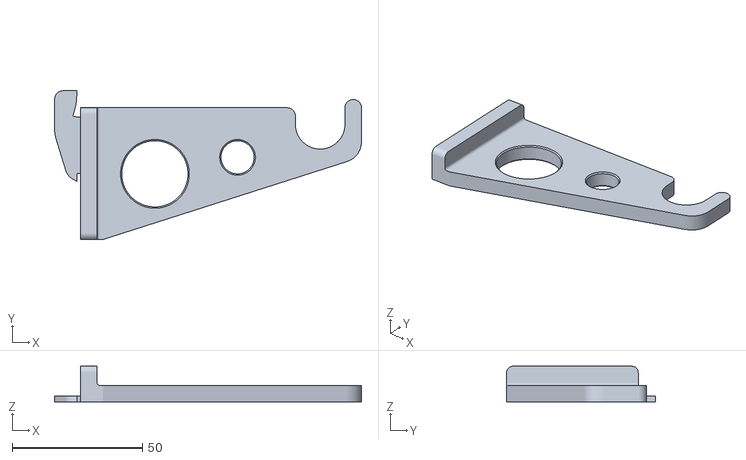
[picture p93: CAD file, 2020-12-05]
Sidepieces/Dowel_rod_hanger/2x4 3-4in Dowel Rod Hanger Left.stl
118.0 x 57.2 x 13.7
