aderusha/DDD-Printable-Wall-Control-System/Sidepieces/Flats/8x0 Flat Left.stl

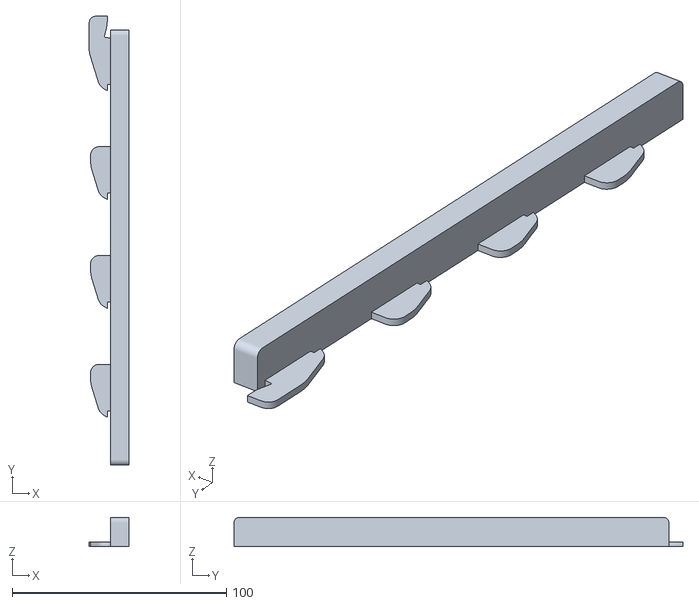
[picture p94: CAD file, 2022-10-10]
Sidepieces/Flats/8x0 Flat Left.stl
18.7 x 209.6 x 13.7
