aderusha/DDD-Printable-Wall-Control-System/Sidepieces/L_brackets/2x1 L Bracket Flat Midmount Left.stl

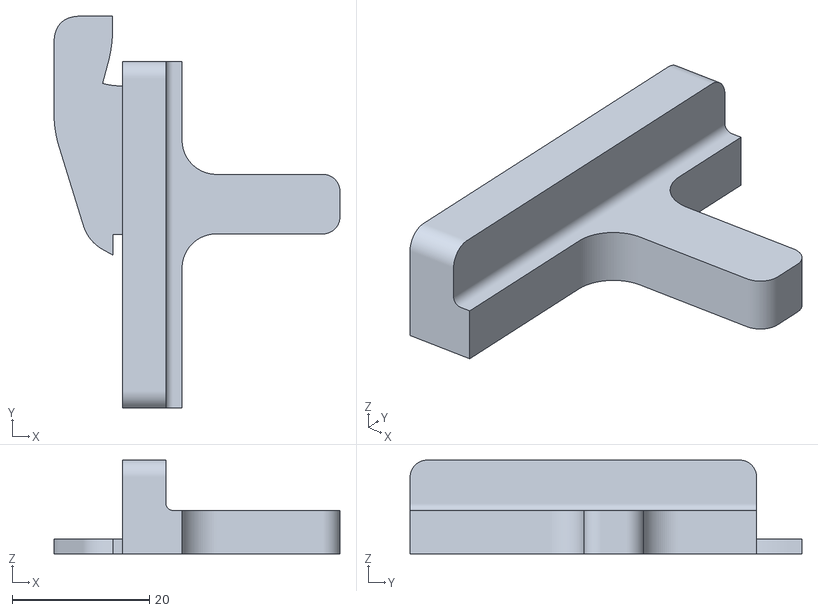
[picture p95: CAD file, 2024-03-11]
Sidepieces/L_brackets/2x1 L Bracket Flat Midmount Left.stl
41.8 x 57.2 x 13.7
