aderusha/DDD-Printable-Wall-Control-System/Sidepieces/Retainers/5x1 Locking Retainer.stl

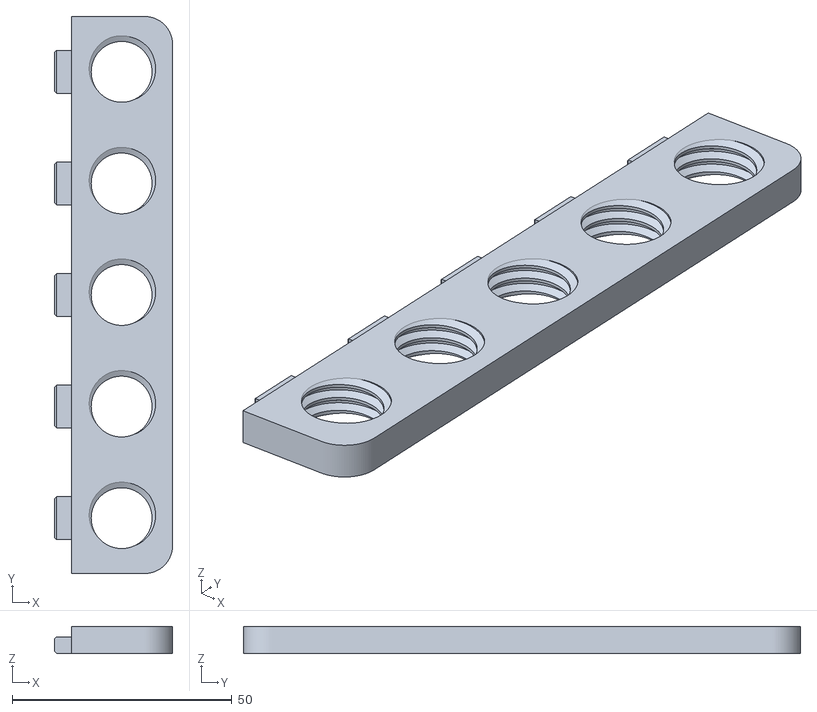
[picture p96: CAD file, 2020-12-05]
Sidepieces/Retainers/5x1 Locking Retainer.stl
26.9 x 126.8 x 6.15
