aderusha/DDD-Printable-Wall-Control-System/Sidepieces/Square_brackets/2x2.25 Square Bracket Flat Center.stl

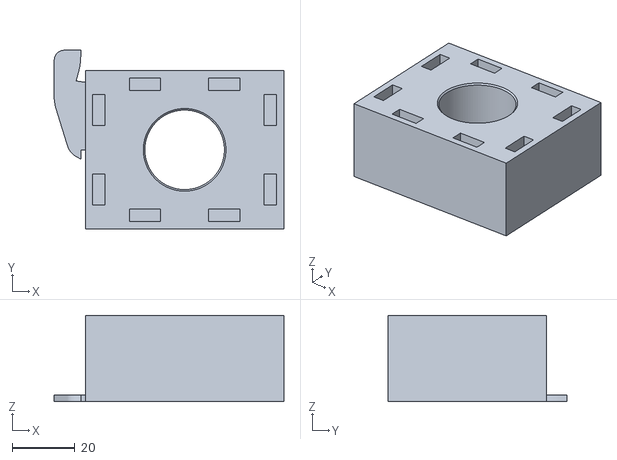
[picture p97: CAD file, 2020-12-05]
Sidepieces/Square_brackets/2x2.25 Square Bracket Flat Center.stl
73.5 x 57.2 x 27.6
