aderusha/DDD-Printable-Wall-Control-System/Centerpieces/Gridfinity/4x2 Gridfinity Frame 2x1.stl

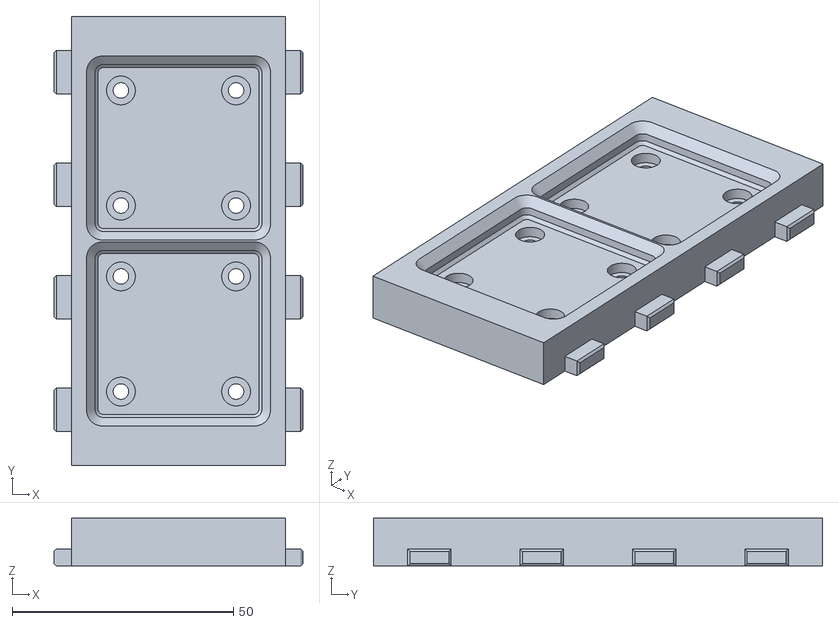
[picture p98: CAD file, 2022-08-01]
Centerpieces/Gridfinity/4x2 Gridfinity Frame 2x1.stl
56.2 x 101.4 x 10.8
