aderusha/DDD-Printable-Wall-Control-System/Centerpieces/Locking_spacer/1x11 Locking Spacer.stl

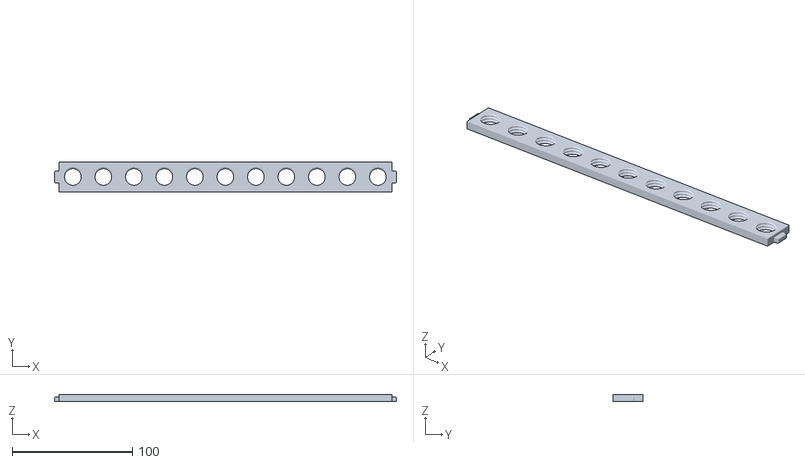
[picture p99: CAD file, 2023-10-14]
Centerpieces/Locking_spacer/1x11 Locking Spacer.stl
284.8 x 25.2 x 6.15
