aderusha/DDD-Printable-Wall-Control-System/Centerpieces/Spacer_blank/4x1 Spacer blank.stl

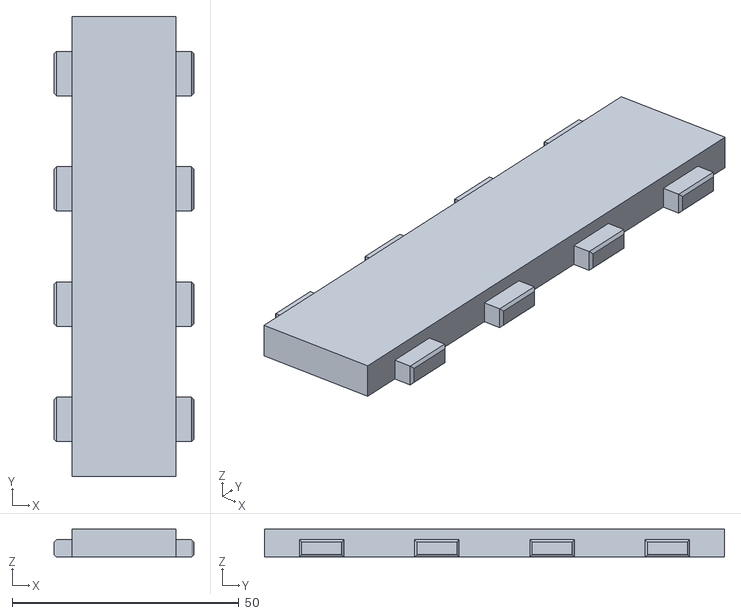
[picture p100: CAD file, 2021-10-13]
Centerpieces/Spacer_blank/4x1 Spacer blank.stl
30.8 x 101.4 x 6.15
