aderusha/DDD-Printable-Wall-Control-System/Centerpieces/Spacer_blank_flush/3x7 Spacer blank flush.stl

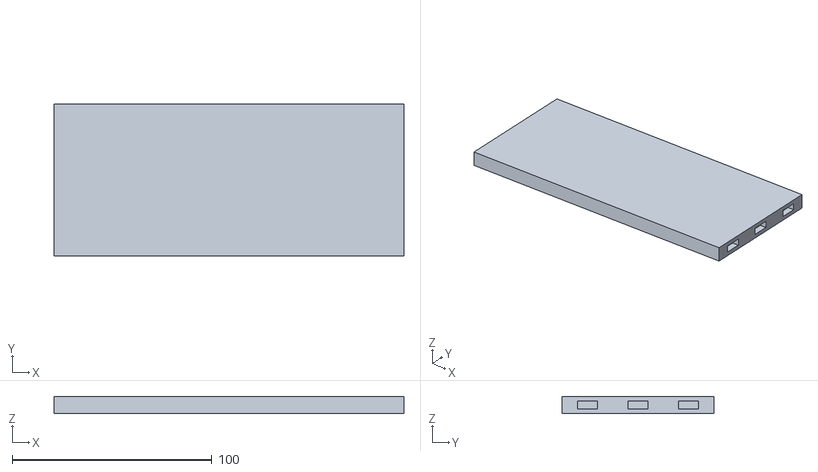
[picture p101: CAD file, 2020-11-09]
Centerpieces/Spacer_blank_flush/3x7 Spacer blank flush.stl
175.4 x 76.0 x 8.70
