aderusha/DDD-Printable-Wall-Control-System/Centerpieces/Spacer_clip-on/2x4 Spacer clip-on.stl

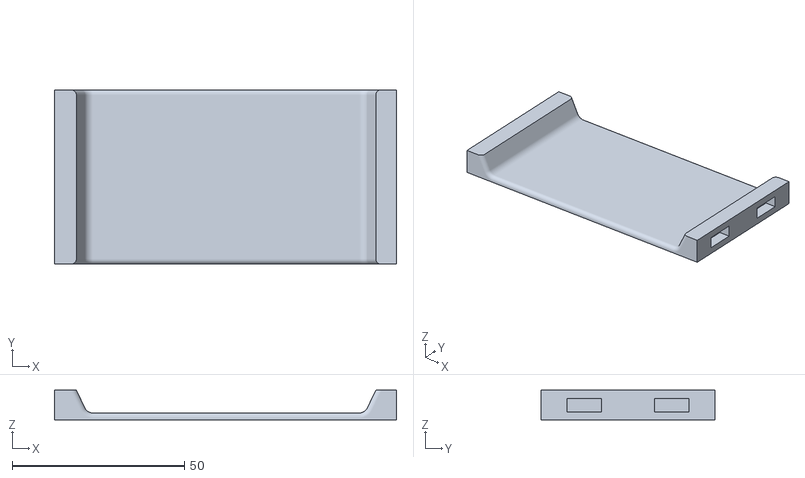
[picture p102: CAD file, 2020-11-09]
Centerpieces/Spacer_clip-on/2x4 Spacer clip-on.stl
99.2 x 50.6 x 8.60
