aderusha/DDD-Printable-Wall-Control-System/Centerpieces/Spacer_perforated/3x6 Spacer perforated.stl

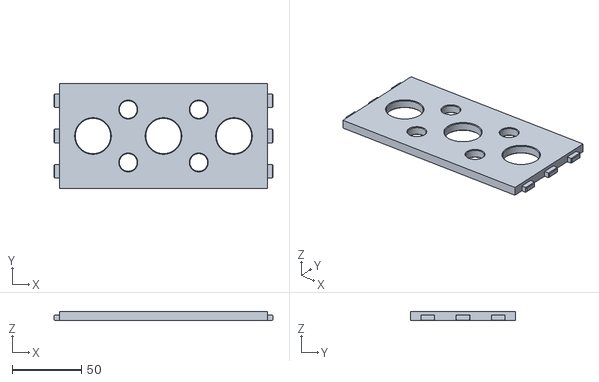
[picture p103: CAD file, 2020-11-09]
Centerpieces/Spacer_perforated/3x6 Spacer perforated.stl
157.8 x 76.0 x 6.15
