aderusha/DDD-Printable-Wall-Control-System/Centerpieces/Tool_hooks/2x1 Firstinfo Air Gun.stl

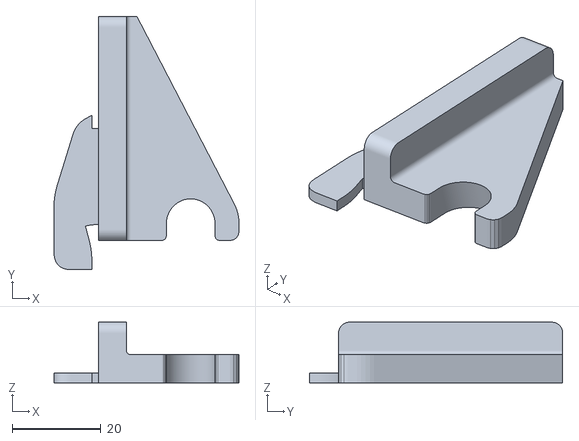
[picture p104: CAD file, 2024-01-18]
Centerpieces/Tool_hooks/2x1 Firstinfo Air Gun.stl
41.8 x 57.2 x 13.7
