aderusha/DDD-Printable-Wall-Control-System/Centerpieces/U_hooks/3x1 10mm U hook.stl

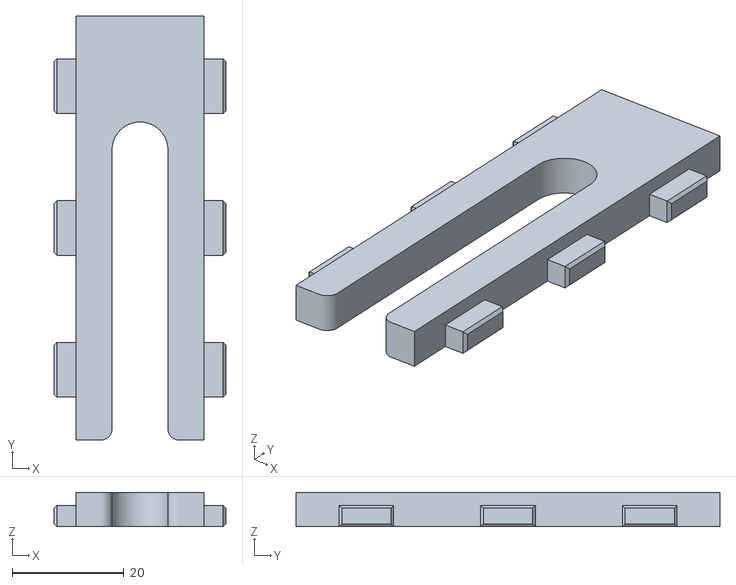
[picture p105: CAD file, 2020-11-23]
Centerpieces/U_hooks/3x1 10mm U hook.stl
30.8 x 76.0 x 6.15
