aderusha/DDD-Printable-Wall-Control-System/Sidepieces/Angle_brackets1/2x4 Angle Bracket Left.stl

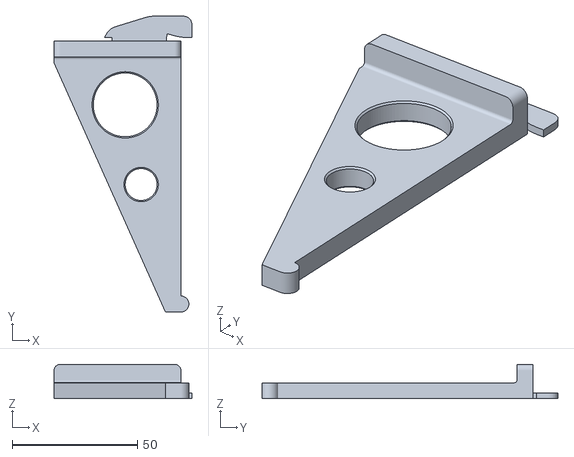
[picture p108: CAD file, 2020-11-10]
Sidepieces/Angle_brackets1/2x4 Angle Bracket Left.stl
55.0 x 118.0 x 13.7
