aderusha/DDD-Printable-Wall-Control-System/Sidepieces/Dowel_rod_hanger/2x4 3-4in Dowel Rod Hanger Center.stl

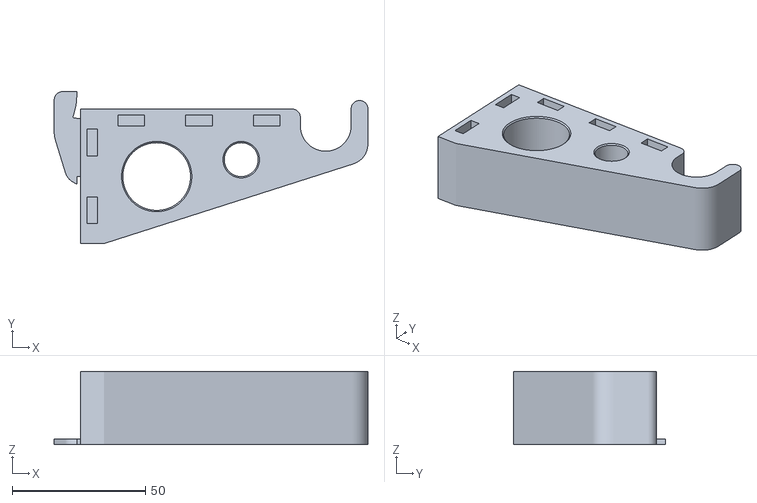
[picture p109: CAD file, 2020-12-05]
Sidepieces/Dowel_rod_hanger/2x4 3-4in Dowel Rod Hanger Center.stl
118.0 x 57.2 x 27.6
