aderusha/DDD-Printable-Wall-Control-System/Sidepieces/Flats/6x0 Flat Center.stl

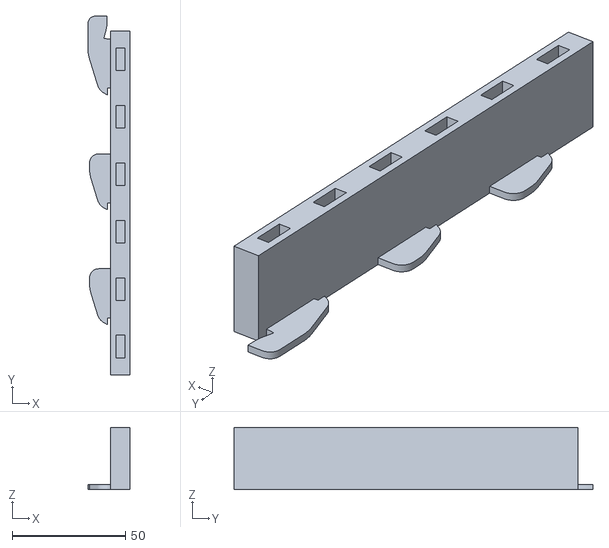
[picture p110: CAD file, 2022-10-10]
Sidepieces/Flats/6x0 Flat Center.stl
18.7 x 158.8 x 27.6
