aderusha/DDD-Printable-Wall-Control-System/Sidepieces/L_brackets/2x2 L Bracket Flat Midmount Right.stl

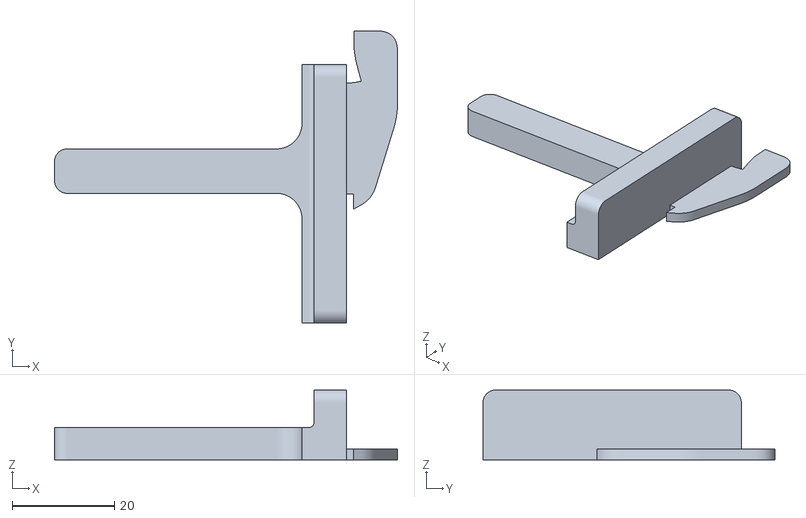
[picture p111: CAD file, 2024-03-11]
Sidepieces/L_brackets/2x2 L Bracket Flat Midmount Right.stl
67.2 x 57.2 x 13.7
