aderusha/DDD-Printable-Wall-Control-System/Sidepieces/Retainers/6x0 Retainer.stl

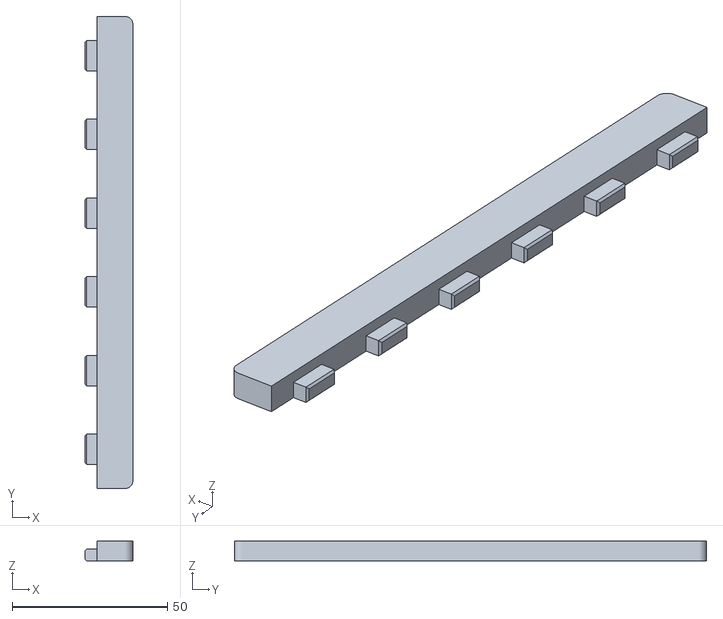
[picture p112: CAD file, 2020-12-05]
Sidepieces/Retainers/6x0 Retainer.stl
15.4 x 152.2 x 6.35
