aderusha/DDD-Printable-Wall-Control-System/Sidepieces/Square_brackets/2x4.25 Square Bracket Hook Center.stl

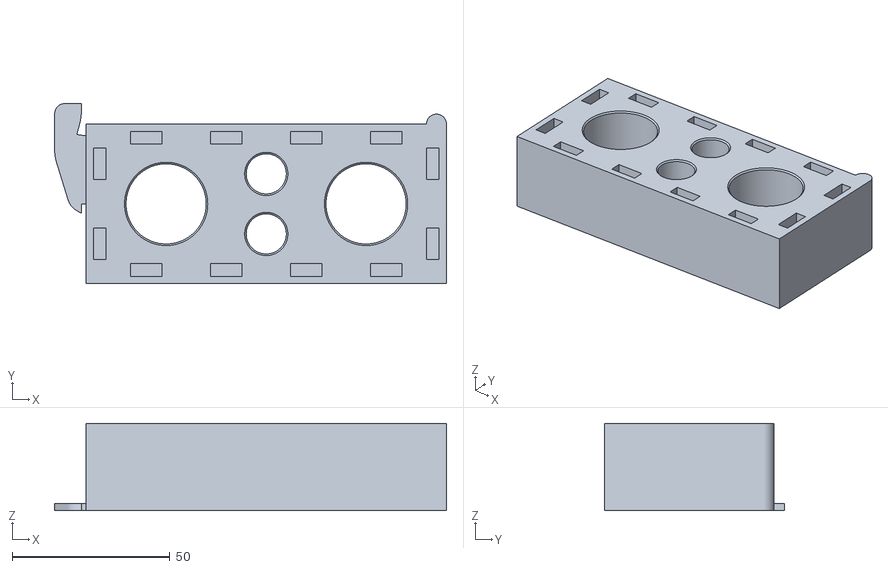
[picture p113: CAD file, 2020-12-05]
Sidepieces/Square_brackets/2x4.25 Square Bracket Hook Center.stl
124.3 x 57.2 x 27.6
