aderusha/DDD-Printable-Wall-Control-System/Centerpieces/Gridfinity/2x6 Gridfinity Frame 1x3.stl

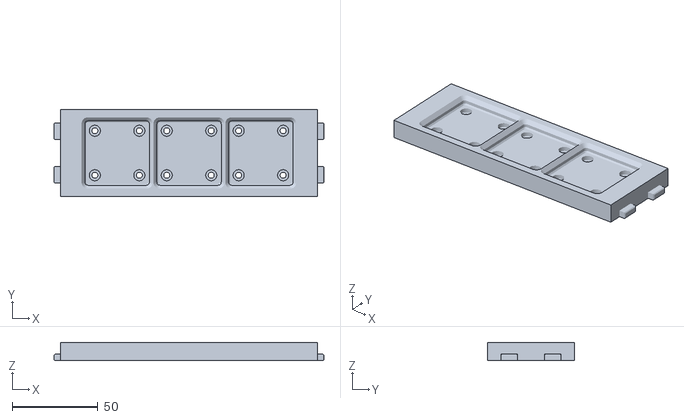
[picture p115: CAD file, 2022-08-01]
Centerpieces/Gridfinity/2x6 Gridfinity Frame 1x3.stl
157.8 x 50.6 x 10.8
