aderusha/DDD-Printable-Wall-Control-System/Centerpieces/Locking_spacer/1x6 Locking Spacer.stl

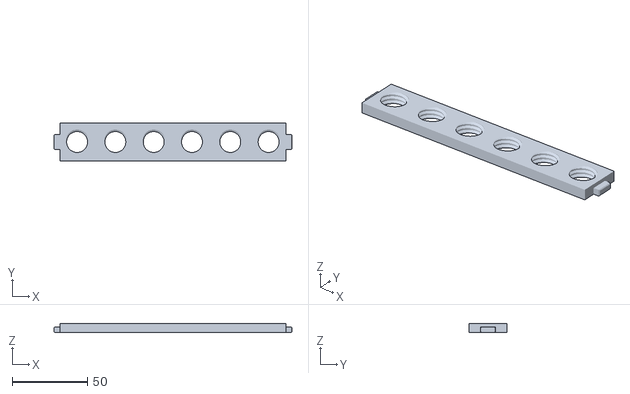
[picture p116: CAD file, 2020-12-05]
Centerpieces/Locking_spacer/1x6 Locking Spacer.stl
157.8 x 25.2 x 6.15
