aderusha/DDD-Printable-Wall-Control-System/Centerpieces/Spacer_blank/4x2 Spacer blank.stl

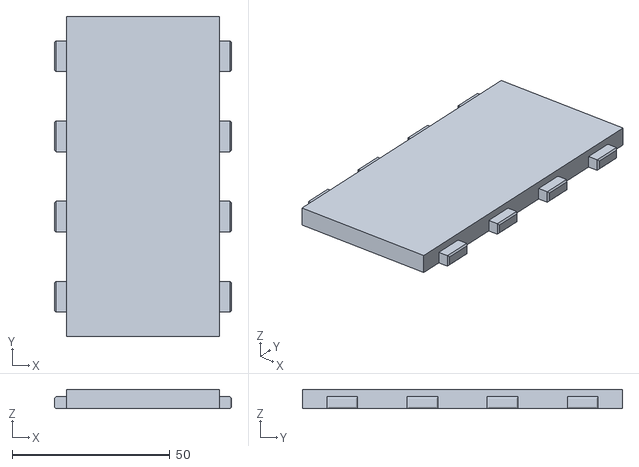
[picture p117: CAD file, 2021-10-13]
Centerpieces/Spacer_blank/4x2 Spacer blank.stl
56.2 x 101.4 x 6.15
