aderusha/DDD-Printable-Wall-Control-System/Centerpieces/Spacer_blank_flush/2x4 Spacer blank flush.stl

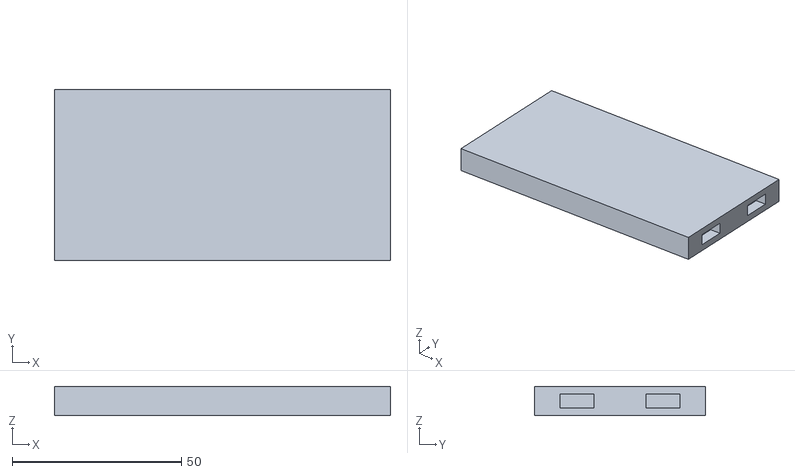
[picture p118: CAD file, 2020-11-09]
Centerpieces/Spacer_blank_flush/2x4 Spacer blank flush.stl
99.2 x 50.6 x 8.70
