aderusha/DDD-Printable-Wall-Control-System/Centerpieces/Spacer_clip-on/2x6 Spacer clip-on.stl

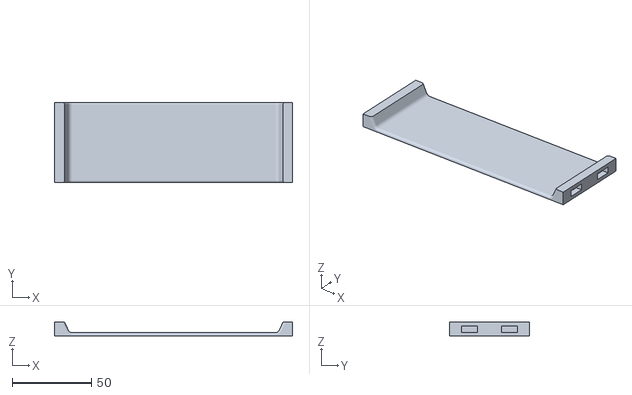
[picture p119: CAD file, 2020-11-09]
Centerpieces/Spacer_clip-on/2x6 Spacer clip-on.stl
150.0 x 50.6 x 8.60
