aderusha/DDD-Printable-Wall-Control-System/Centerpieces/Spacer_perforated/2x7 Spacer perforated.stl

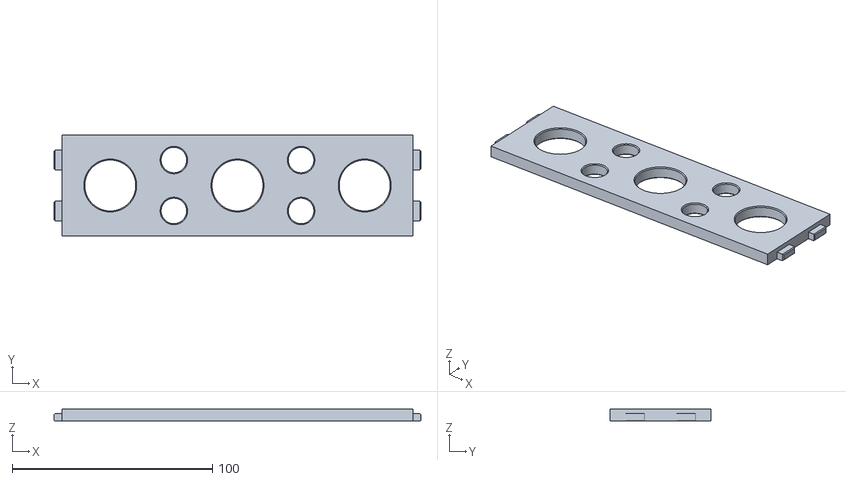
[picture p120: CAD file, 2020-11-09]
Centerpieces/Spacer_perforated/2x7 Spacer perforated.stl
183.2 x 50.6 x 6.15
