aderusha/DDD-Printable-Wall-Control-System/Centerpieces/Tool_hooks/3x4 DeWalt DCG414 4.5in 60v Grinder.stl

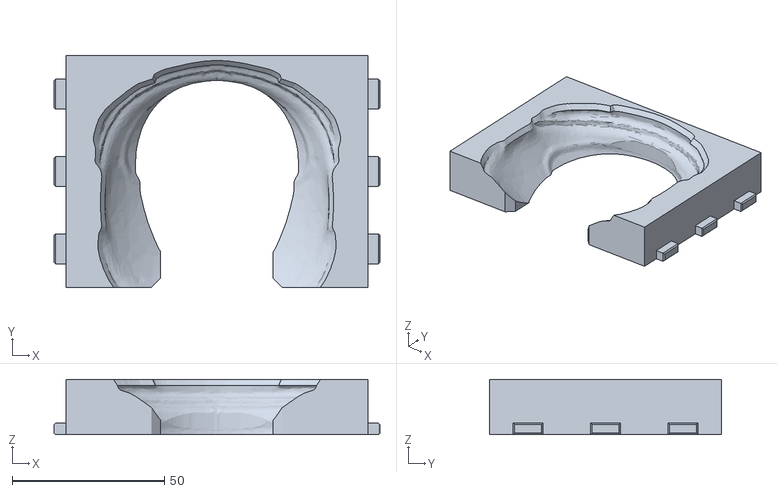
[picture p121: CAD file, 2024-01-18]
Centerpieces/Tool_hooks/3x4 DeWalt DCG414 4.5in 60v Grinder.stl
107.0 x 76.0 x 18.1
