aderusha/DDD-Printable-Wall-Control-System/Centerpieces/U_hooks/2x4 2x 42.5mm U hooks.stl

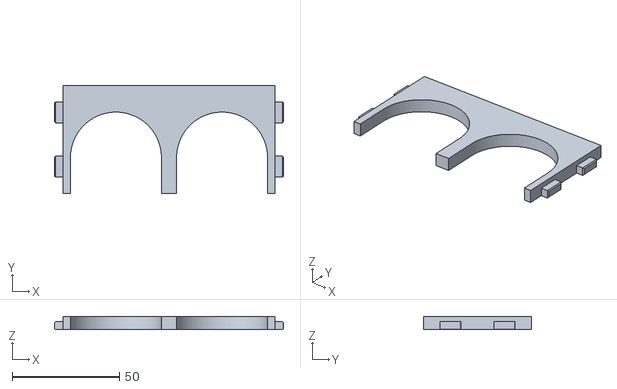
[picture p122: CAD file, 2020-11-10]
Centerpieces/U_hooks/2x4 2x 42.5mm U hooks.stl
107.0 x 50.6 x 6.15
