aderusha/DDD-Printable-Wall-Control-System/Sidepieces/Angle_brackets/3x7 Angle Bracket Flat Center.stl

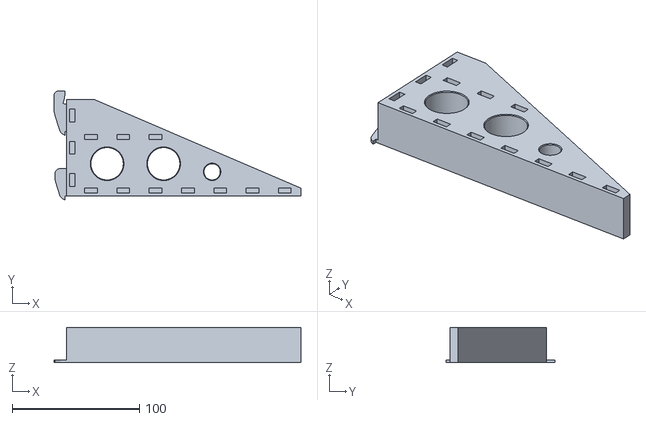
[picture p123: CAD file, 2023-10-14]
Sidepieces/Angle_brackets/3x7 Angle Bracket Flat Center.stl
194.1 x 85.7 x 27.6
