aderusha/DDD-Printable-Wall-Control-System/Sidepieces/Angle_brackets1/2x3 Angle Bracket Center.stl

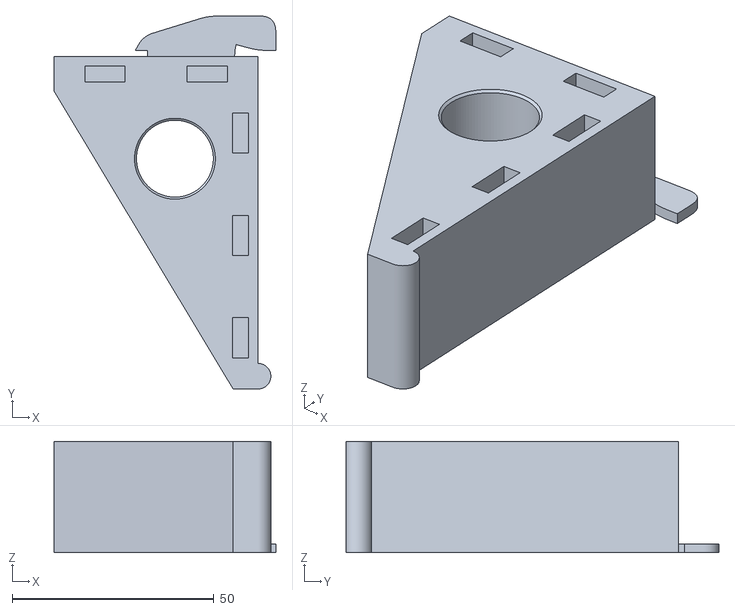
[picture p124: CAD file, 2020-11-10]
Sidepieces/Angle_brackets1/2x3 Angle Bracket Center.stl
55.0 x 92.5 x 27.6
