aderusha/DDD-Printable-Wall-Control-System/Sidepieces/Flats/7x0 Flat Left.stl

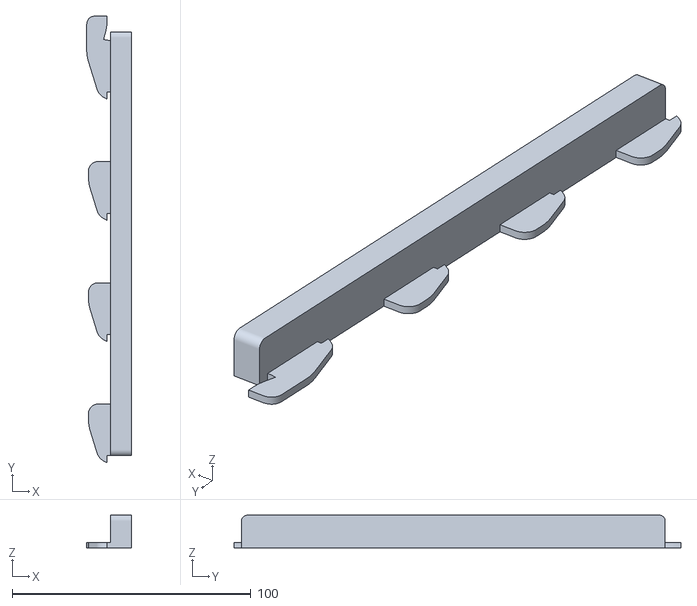
[picture p125: CAD file, 2022-10-10]
Sidepieces/Flats/7x0 Flat Left.stl
18.7 x 187.3 x 13.7
