aderusha/DDD-Printable-Wall-Control-System/Sidepieces/L_brackets/2x3 L Bracket Flat Midmount Left.stl

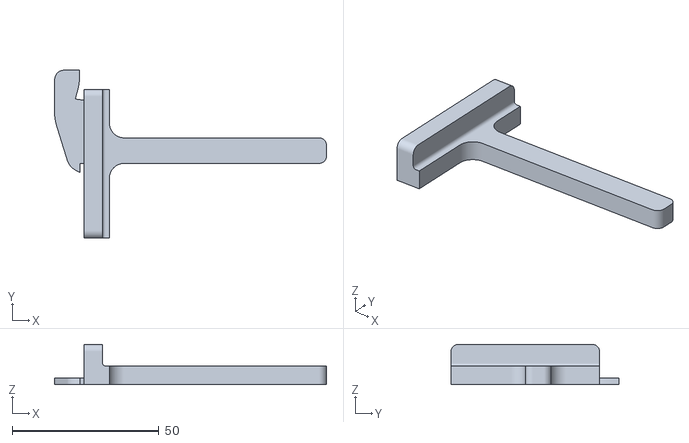
[picture p126: CAD file, 2024-03-11]
Sidepieces/L_brackets/2x3 L Bracket Flat Midmount Left.stl
92.6 x 57.2 x 13.7
