aderusha/DDD-Printable-Wall-Control-System/Sidepieces/Retainers/3x0 Retainer.stl

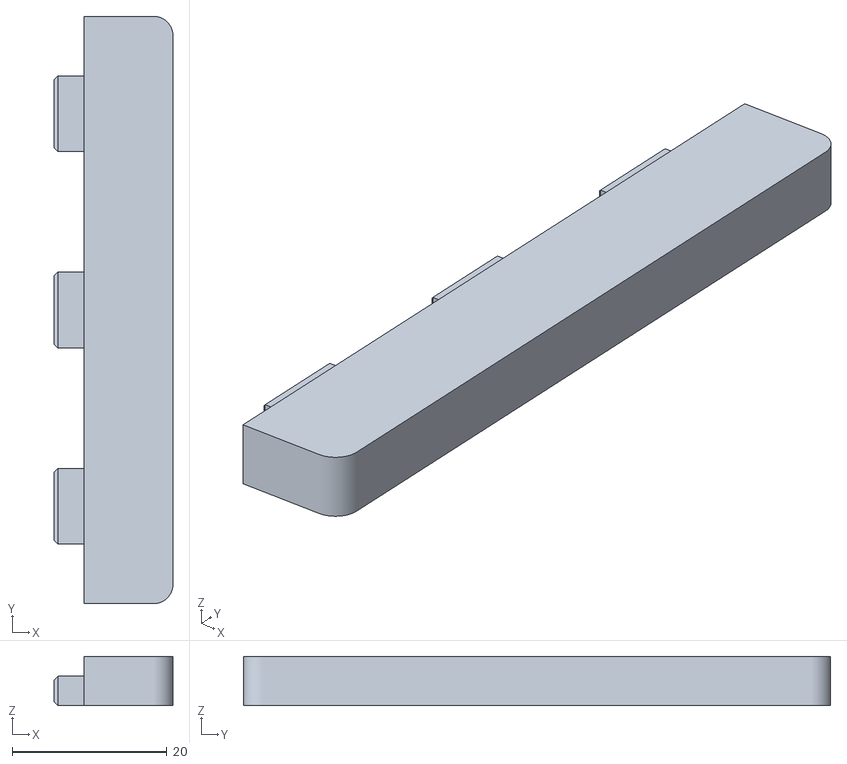
[picture p127: CAD file, 2020-12-05]
Sidepieces/Retainers/3x0 Retainer.stl
15.4 x 76.0 x 6.35
