aderusha/DDD-Printable-Wall-Control-System/Accessories/4x10x8mm Pin.stl

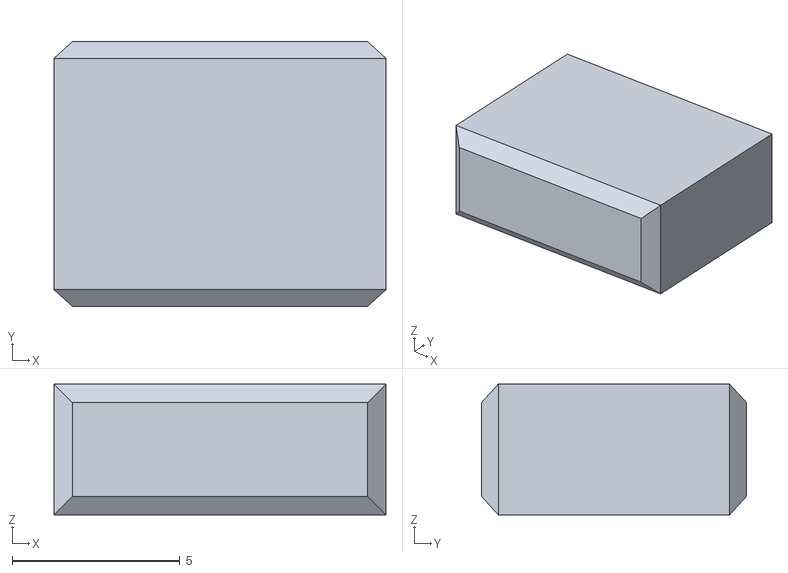
[picture p131: CAD file, 2020-12-05]
Accessories/4x10x8mm Pin.stl
9.90 x 7.90 x 3.90
