aderusha/DDD-Printable-Wall-Control-System/Centerpieces/Gridfinity/2x4 Gridfinity Frame 1x2.stl

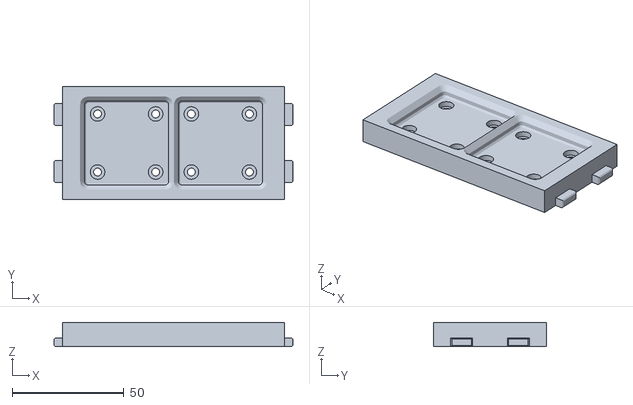
[picture p132: CAD file, 2022-08-01]
Centerpieces/Gridfinity/2x4 Gridfinity Frame 1x2.stl
107.0 x 50.6 x 10.8
