aderusha/DDD-Printable-Wall-Control-System/Centerpieces/Locking_spacer/3x5 Locking Spacer.stl

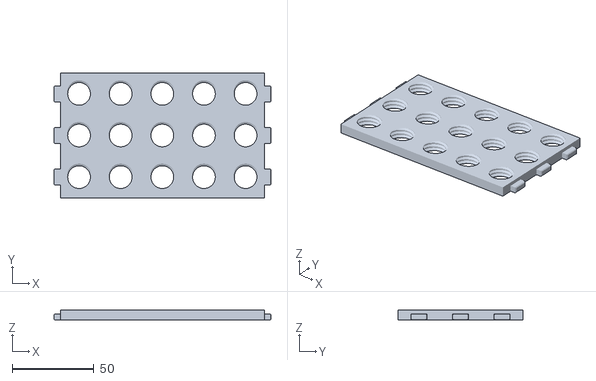
[picture p133: CAD file, 2020-12-05]
Centerpieces/Locking_spacer/3x5 Locking Spacer.stl
132.4 x 76.0 x 6.15
