aderusha/DDD-Printable-Wall-Control-System/Centerpieces/Spacer_blank/4x4 Spacer blank.stl

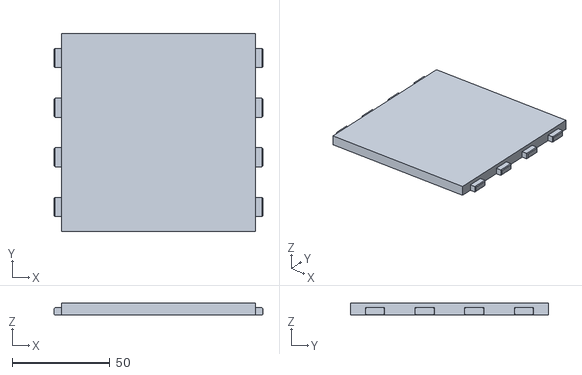
[picture p134: CAD file, 2021-10-13]
Centerpieces/Spacer_blank/4x4 Spacer blank.stl
107.0 x 101.4 x 6.15
