aderusha/DDD-Printable-Wall-Control-System/Centerpieces/Spacer_blank_flush/3x2 Spacer blank flush.stl

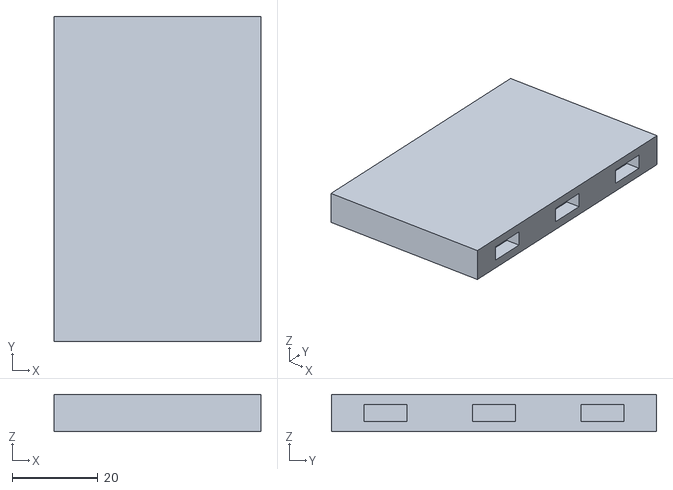
[picture p135: CAD file, 2020-11-09]
Centerpieces/Spacer_blank_flush/3x2 Spacer blank flush.stl
48.4 x 76.0 x 8.70
