aderusha/DDD-Printable-Wall-Control-System/Centerpieces/Spacer_clip-on/3x2 Spacer clip-on.stl

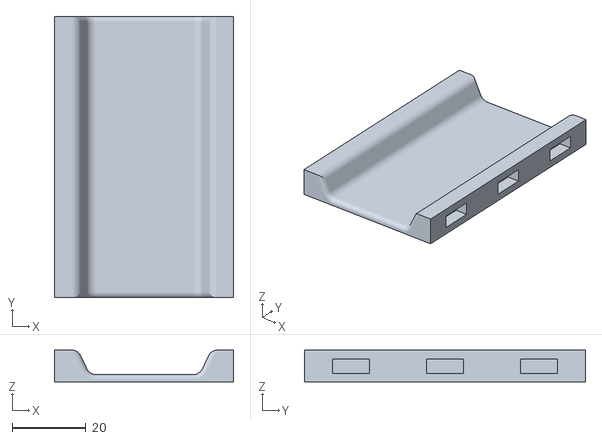
[picture p136: CAD file, 2020-11-09]
Centerpieces/Spacer_clip-on/3x2 Spacer clip-on.stl
48.4 x 76.0 x 8.60
