aderusha/DDD-Printable-Wall-Control-System/Centerpieces/Spacer_perforated/3x3 Spacer perforated.stl

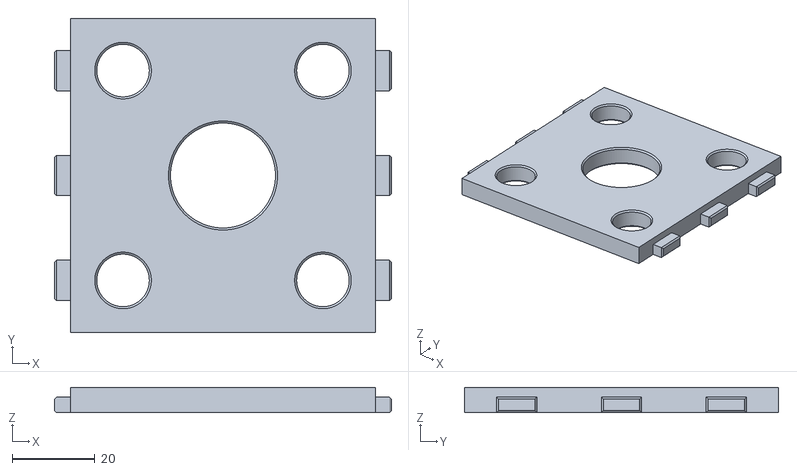
[picture p137: CAD file, 2020-11-09]
Centerpieces/Spacer_perforated/3x3 Spacer perforated.stl
81.6 x 76.0 x 6.15
