aderusha/DDD-Printable-Wall-Control-System/Centerpieces/Tool_hooks/3x4 DeWalt DCG440 7in 60v Grinder.stl

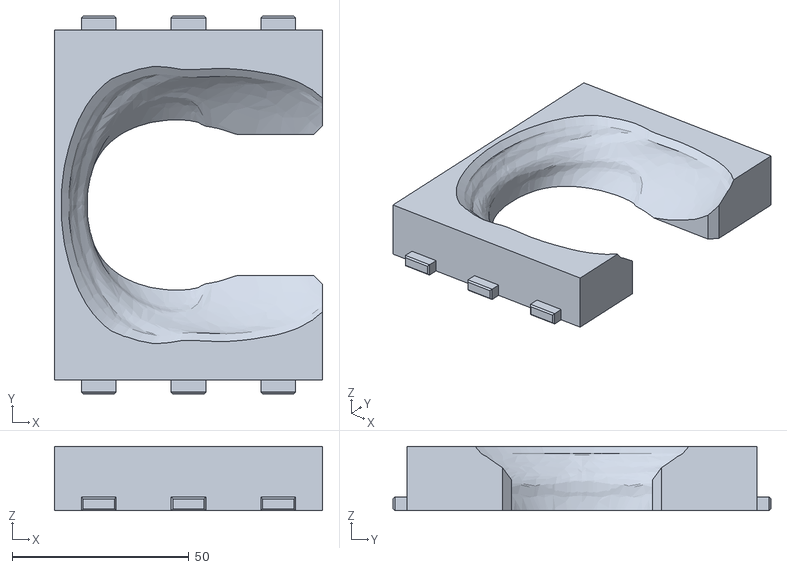
[picture p138: CAD file, 2024-01-18]
Centerpieces/Tool_hooks/3x4 DeWalt DCG440 7in 60v Grinder.stl
76.0 x 107.0 x 18.2
