aderusha/DDD-Printable-Wall-Control-System/Quickhooks/Quickhook 2in Heavy.stl

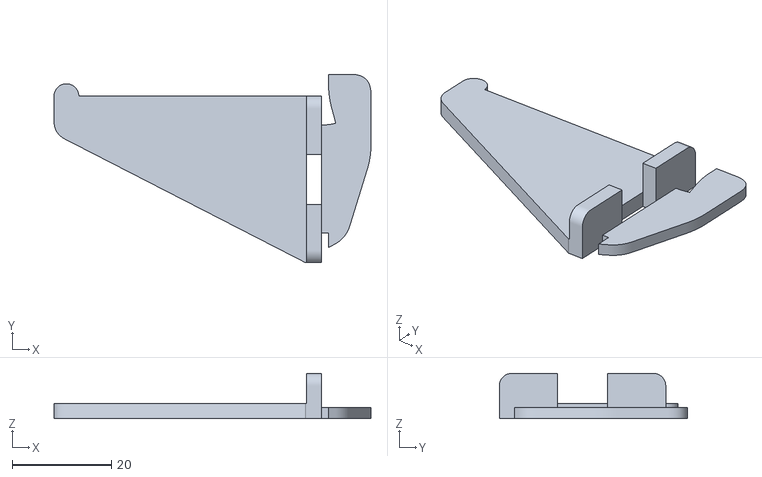
[picture p140: CAD file, 2020-11-10]
Quickhooks/Quickhook 2in Heavy.stl
63.8 x 37.9 x 9.10
