aderusha/DDD-Printable-Wall-Control-System/Sidepieces/L_brackets/2x3 L Bracket Flat Midmount Center.stl

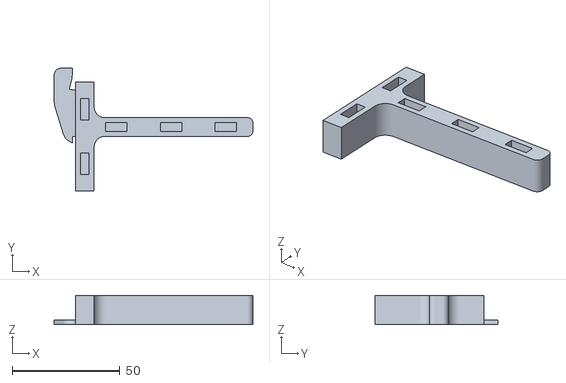
[picture p142: CAD file, 2024-03-11]
Sidepieces/L_brackets/2x3 L Bracket Flat Midmount Center.stl
92.5 x 57.2 x 13.7
