aderusha/DDD-Printable-Wall-Control-System/Sidepieces/Retainers/4x0 Retainer.stl

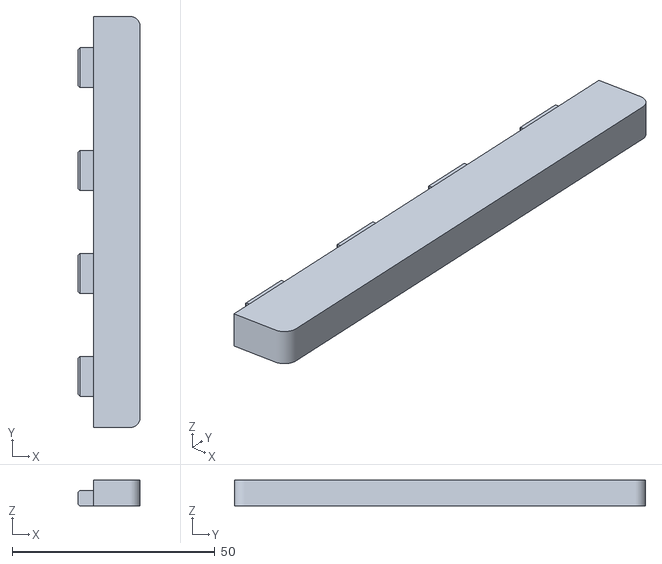
[picture p143: CAD file, 2020-12-05]
Sidepieces/Retainers/4x0 Retainer.stl
15.4 x 101.4 x 6.35
