aderusha/DDD-Printable-Wall-Control-System/Sidepieces/U_brackets/3x4.25 4in U Bracket Center .stl

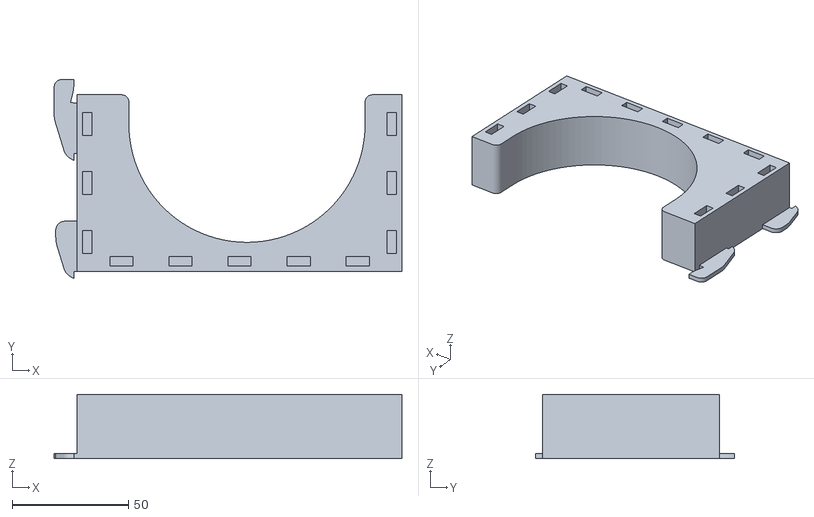
[picture p144: CAD file, 2022-08-23]
Sidepieces/U_brackets/3x4.25 4in U Bracket Center .stl
149.7 x 85.7 x 27.6
