aderusha/DDD-Printable-Wall-Control-System/Accessories/8mm Lock Pin.stl

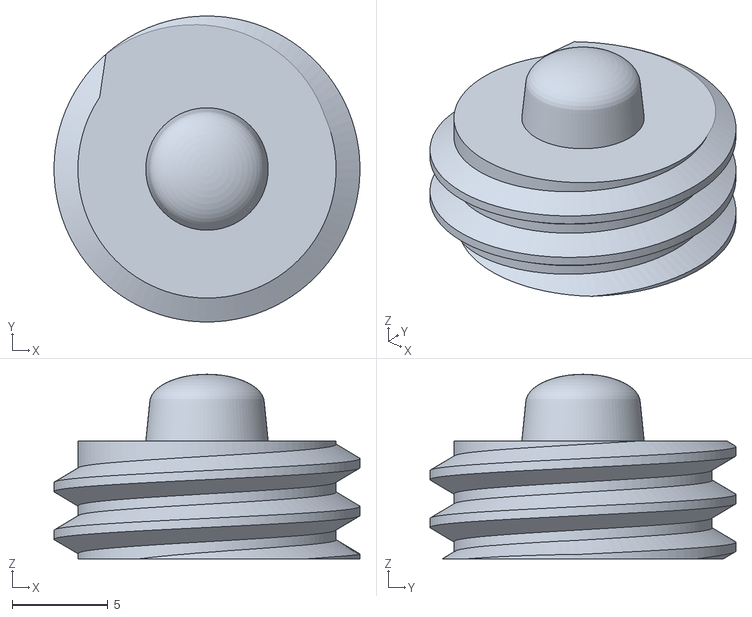
[picture p145: CAD file, 2020-12-05]
Accessories/8mm Lock Pin.stl
16.0 x 16.0 x 9.65
