aderusha/DDD-Printable-Wall-Control-System/Centerpieces/Gridfinity/2x2 Gridfinity Frame 1x1.stl

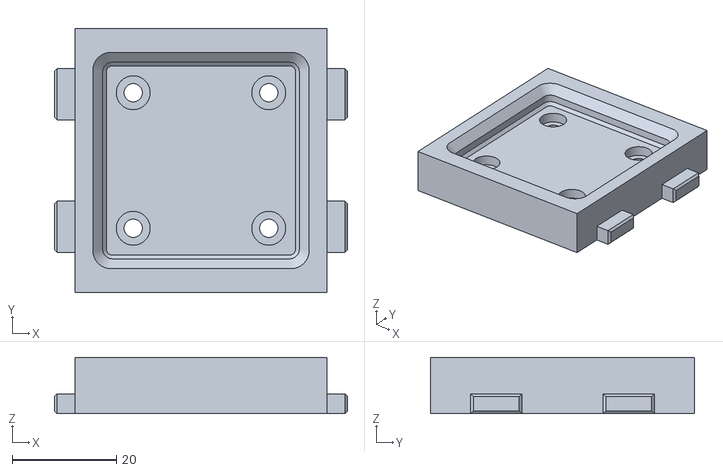
[picture p146: CAD file, 2022-08-01]
Centerpieces/Gridfinity/2x2 Gridfinity Frame 1x1.stl
56.2 x 50.6 x 10.8
