aderusha/DDD-Printable-Wall-Control-System/Centerpieces/Locking_spacer/3x1 Locking Spacer.stl

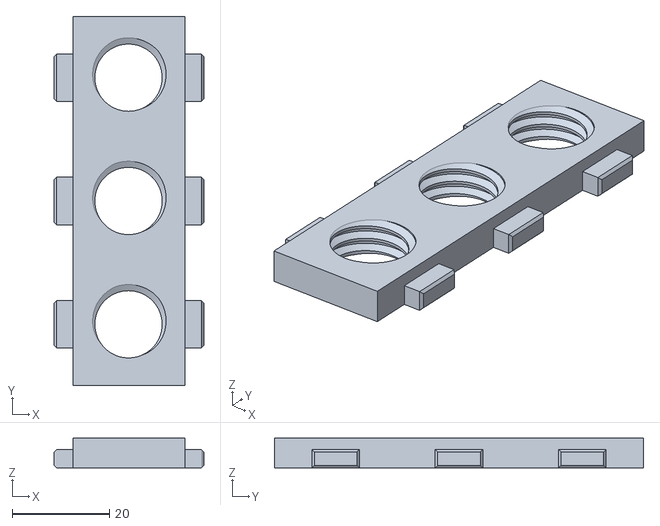
[picture p147: CAD file, 2020-12-05]
Centerpieces/Locking_spacer/3x1 Locking Spacer.stl
30.8 x 76.0 x 6.15
