aderusha/DDD-Printable-Wall-Control-System/Centerpieces/Spacer_blank/1x1 Spacer blank.stl

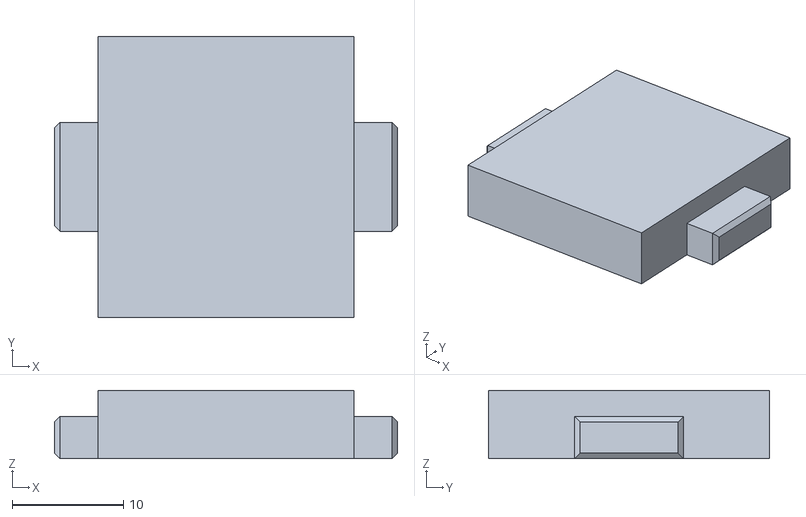
[picture p148: CAD file, 2020-12-05]
Centerpieces/Spacer_blank/1x1 Spacer blank.stl
30.8 x 25.2 x 6.15
