aderusha/DDD-Printable-Wall-Control-System/Centerpieces/Spacer_blank_flush/2x7 Spacer blank flush.stl

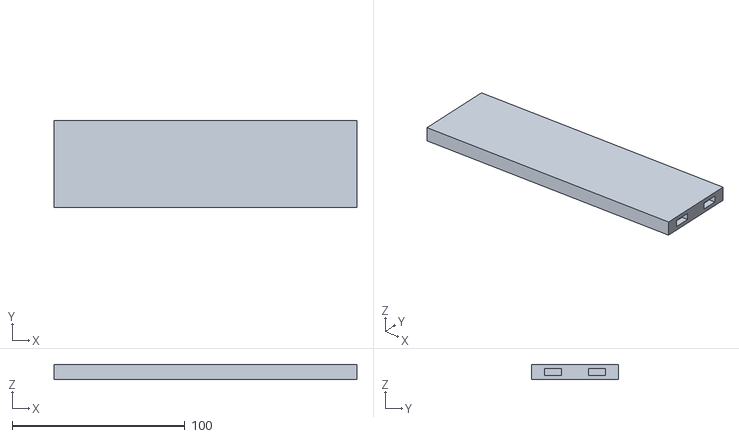
[picture p149: CAD file, 2020-11-09]
Centerpieces/Spacer_blank_flush/2x7 Spacer blank flush.stl
175.4 x 50.6 x 8.70
