aderusha/DDD-Printable-Wall-Control-System/Centerpieces/Spacer_clip-on/3x5 Spacer clip-on.stl

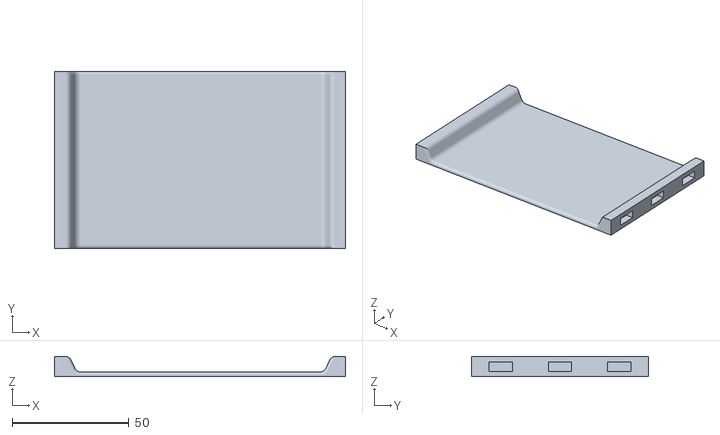
[picture p150: CAD file, 2020-11-09]
Centerpieces/Spacer_clip-on/3x5 Spacer clip-on.stl
124.6 x 76.0 x 8.60
