aderusha/DDD-Printable-Wall-Control-System/Centerpieces/U_hooks/2x2 1.5in U hook.stl

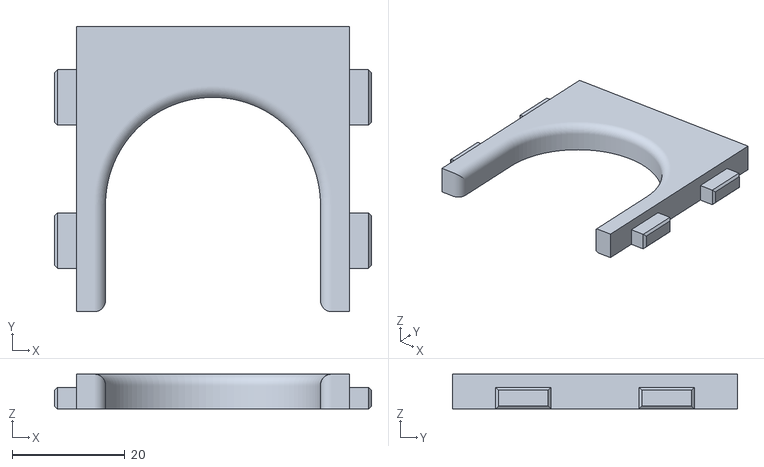
[picture p152: CAD file, 2020-11-10]
Centerpieces/U_hooks/2x2 1.5in U hook.stl
56.2 x 50.6 x 6.15
