aderusha/DDD-Printable-Wall-Control-System/Quickhooks/Quickhook 3in Heavy.stl

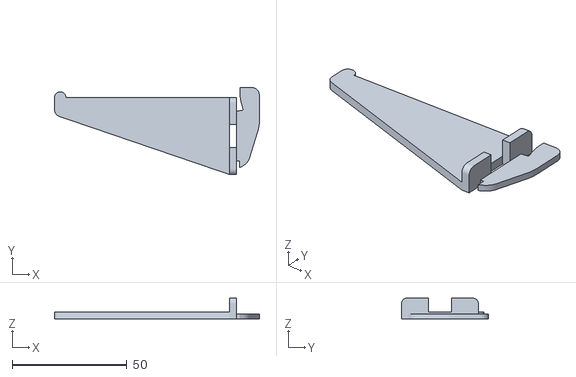
[picture p153: CAD file, 2020-11-10]
Quickhooks/Quickhook 3in Heavy.stl
89.2 x 37.9 x 9.10
