aderusha/DDD-Printable-Wall-Control-System/Sidepieces/Angle_brackets/3x8 Angle Bracket Inverted Flat Right.stl

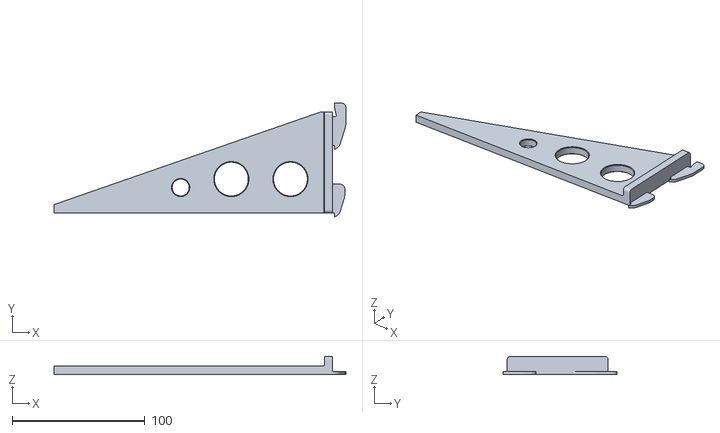
[picture p154: CAD file, 2022-08-23]
Sidepieces/Angle_brackets/3x8 Angle Bracket Inverted Flat Right.stl
219.5 x 85.7 x 13.7
