aderusha/DDD-Printable-Wall-Control-System/Sidepieces/Angle_brackets1/4x4 Angle Bracket Center.stl

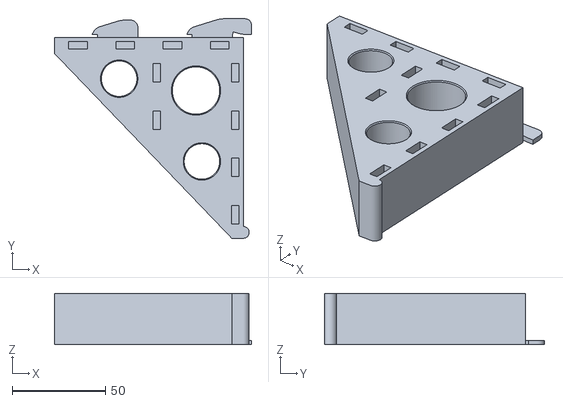
[picture p155: CAD file, 2020-11-10]
Sidepieces/Angle_brackets1/4x4 Angle Bracket Center.stl
105.8 x 118.0 x 27.6
